micromouseonline/kronos/hesperus-timing-gate/docs/review.md

# Technical Review: KRONOS/CERBERUS Gate Firmware

`hesperus-timing-gate/firmware/src/main.cpp`

Reviewed by Claude

---

## Outstanding Features

### Disciplined dual-clock holdover architecture
The most technically sophisticated element of the firmware. By simultaneously capturing
both the Wi-Fi TSF counter and `esp_timer_get_time()` in the ISR at the moment of
the physical trigger, the design mirrors the holdover architecture of a professional
GPS receiver: a primary reference (TSF, disciplined by the AP's hardware beacon) and a
fallback oscillator (CPU crystal, disciplined by the EMA-filtered `clock_alpha`).
This is exactly the right approach for a wireless timing system where the primary
reference can momentarily disappear.

### EMA-filtered clock_alpha calibration
The 10%/90% EMA on `clock_alpha` is well-chosen. It suppresses per-beacon jitter while
still tracking slow crystal drift over minutes and hours. The >4 s inter-sample gate
ensures the ratio is statistically stable before being fed into the filter, avoiding
contamination from back-to-back events.

### MIN_PLAUSIBLE_TSF plausibility guard (300 000 000 µs)
Prevents accepting a TSF captured in the narrow window after a Wi-Fi stack reset before
beacon resynchronisation has occurred. 300 seconds is a well-judged threshold: long
enough to be certain the stack is settled, short enough to not delay legitimate startup.

### Escape hatch (PATCH 1) — proactive SYN recovery
After a successful `200 OK` response during SYN mode, the firmware immediately queries
the raw TSF and, if it looks healthy, forces re-entry by resetting `has_initial_baseline`.
This is a clean, proactive mechanism that does not rely on a new trigger event to
initiate recovery — important in a low-traffic test scenario where gate events may be
sparse.

### Explicit BSSID binding
`WiFi.begin(ssid, password, 0, bssid)` locks association to a known AP. Without this,
the ESP32 may roam to a neighbour access point whose TSF epoch is completely unrelated,
silently corrupting the timing baseline in a way that is very hard to diagnose in the
field.

### Prime heartbeat interval (5147 ms)
A non-round heartbeat interval desynchronises the transmission from 802.11 DTIM beacon
periods and from periodic tasks on other stations, reducing collision probability at the
AP — a detail that most implementors overlook.

### Correct FreeRTOS ISR practice
The beam-sample timer ISR (`onBeamSampleTimer`, `beam-sensor.h`'s dual-EMA
detector) does the minimum possible work: `vTaskNotifyGiveFromISR` followed
by `portYIELD_FROM_ISR()` when needed, nothing else. No ADC read, no float
math, and no queue push happen in ISR context — those are deferred to
`beamSampleTask`, woken by the notification, which does the `analogRead()`s,
runs the detector, and only then calls the plain (non-ISR) `xQueueSend()` to
hand a trigger off to `tsfCaptureTask`. Keeping the ISR to a bare notify is
the right call here specifically because the actual detection work (two
EMA updates plus a ratio compare) is too much to justify running inside an
ISR at all, unlike a simple GPIO edge capture.

### Hard Wi-Fi watchdog
`WiFi.disconnect(true, true)` + delay + `WiFi.begin()` completely tears down and
rebuilds the radio interface. A soft reconnect alone cannot recover certain ESP-IDF
lwIP crash states. This is the correct treatment for a 15-second silence.

---

## Summary Assessment

The dual-clock holdover design is genuinely impressive for a consumer-grade Wi-Fi
platform and represents a level of engineering depth that goes well beyond typical
ESP32 hobby projects. The empirical results (mean gap 2.36 µs, max 55 µs, 100%
pairing over 60,000 events) validate the architecture.

---

## Possible stress tests:

**Status update, 2026-08-06**: the beacon-spam campaign in
`NETWORK-TIMING-LOG.md` (spam-test sessions 2-15a) has since exercised
Layer 1 extensively — via deliberate beacon-frame flooding rather than the
HTTP-GET-flood method sketched below, but the same airtime-saturation
effect — and Layer 3 partially, via Bluetooth audio streaming co-tested
alongside the spammers (sessions 9-10, 15a) as a stand-in for channel
interference. Layers 2 (bulk throughput) and 4 (broadband noise) remain
genuinely untested and are deprioritized (`TODO.md`'s "Congested-airtime
stress testing" item) rather than actively planned. The sketches below are
left as originally written for reference.

  ### Layer 1 — Airtime saturation (your idea, refined)

  20 ESP32s each running a tight loop of HTTP GETs to a local server (a Pi or laptop running a trivial HTTP responder). 
  Set them all to the same SSID/BSSID as the timing gates. The goal is to pack the AP's transmit queue and force beacon 
  deferral — consumer APs do not protect beacon TBTTs under heavy load, so this directly stresses TSF jitter. Metrics 
  to watch: drift_variance in the audit log, and whether consecutive_audit_failures climbs.

  ### Layer 2 — Bulk throughput (saturate the medium)

  A Raspberry Pi (or any laptop) on the same AP running iperf3 -s, with another client doing iperf3 -c <ip> -t 300 
  generates sustained throughput that competes with every other station for airtime. Much higher per-device impact 
  than ESP32 GETs.

  ### Layer 3 — Channel interference (harder to ignore than load)

  A second cheap WiFi router (any old home router) configured to broadcast on an overlapping channel (e.g. your AP on ch 6, 
  the stressor on ch 4 or 8). This generates RF contention the AP cannot back off from, causing collision-driven retries 
  and beacon slippage. Very realistic simulation of a busy sports venue.

  ### Layer 4 — 2.4 GHz broadband noise

  A microwave oven running 30 cm from the AP is a surprisingly effective 2.4 GHz jammer — free if you have one, and 
  recreates the kind of environment you'd find at a car park or sports field.

  ### What to instrument

  The timing gate serial log already shows you drift_variance per event and consecutive_audit_failures. Add a counter 
  to the server side tracking how often mode=SYN appears in requests — that's your headline metric for how badly TSF sync 
  degrades under load. If you get to 5+ consecutive audit failures triggering forced re-baseline, the AP is struggling 
  to deliver beacons reliably.
  
---

## Future Development Path

Updated 2026-08-06: removed three rows that shipped since this table was
written (mDNS server discovery, HTTP keep-alive/WebSocket, and a
diagnostics HTTP server — see `docs/PROVISIONING.md`,
`NETWORK-TIMING-LOG.md`, and `firmware/src/net/debug-http-server.h`/
`network-health-stats.h` respectively) and trimmed "server URL" from the
NVS config store row for the same reason (cerberus's address is now
resolved dynamically via mDNS, not a config-store override). The
diagnostics server (`GET /logs`, `GET /status`, `GET`/`POST /status/reset`)
also covers part of what the old "field-deployable overflow-drop
notification" gap needed — lifetime stall/drop/disconnect counters now
persist across reboot (NVS) and are readable remotely, without a serial
cable attached.

| Phase | Feature | Notes |
|---|---|---|
| Near | Wi-Fi Modem Sleep | Extensively investigated, not just "unblocked" — see `NETWORK-TIMING-LOG.md`'s "Wi-Fi power-save vs. battery budget" issue (sessions 11-15a). `WIFI_PS_NONE` (`main.cpp:869`) stays the shipped default (decided 2026-08-04, ~110mA); `WIFI_PS_MIN_MODEM` saves ~35-40% power but has a real, still-unexplained stall/reliability regression under heavy congestion that got worse after one attempted mitigation. Still the highest-priority open item in that doc |
| Near | NVS config store | gate_id override, BEAM_CONFIRM_SAMPLES, DRIFT_MARGIN_US |
| Near | Configurable confirm-sample count | Per-channel `BEAM_CONFIRM_SAMPLES` (`beam-sensor.h`), loaded from NVS |
| Medium | OTA firmware update | ArduinoOTA or ESP-IDF OTA; critical for field deployment |
| Medium | SSD1306 display task | Gate ID, clock mode, last gap, queue depth (lib already in platformio.ini) |
| Medium | Stack telemetry in heartbeat | Append `&stack=NNN` to HB URL for remote diagnostics; scaffolding exists but is commented out (`main.cpp:510-512`) |
| Long | NVS event buffering | Survive power cycle with unsent events preserved in flash |
| Long | Multi-AP BSSID fallback | Secondary AP list with explicit TSF-resync on AP switch |
| Long | Local standalone scoring | Compute lap/split locally if server unreachable; display on SSD1306 |
| Long | Beam-sensor oversampling (DMA + decimate) | Raise ADC sample rate above 1kHz to reject 500-2000Hz pulsed-light aliasing; deferred 2026-09-09 after a bench trial at >4000lux ambient + heavy 1kHz pulsed interference showed reliable operation with the current 1kHz scheme. Revisit only if field trials later show it's still needed. Investigation notes (oversample-then-decimate via DMA, batched EMA catch-up design) captured for reuse if resumed |
