micromouseonline/kronos/references/ESP32-S3-TINY/ESP32-S3-Tiny-details-1-3cb57dcb7847e1db49d2faee9722d6df.webp

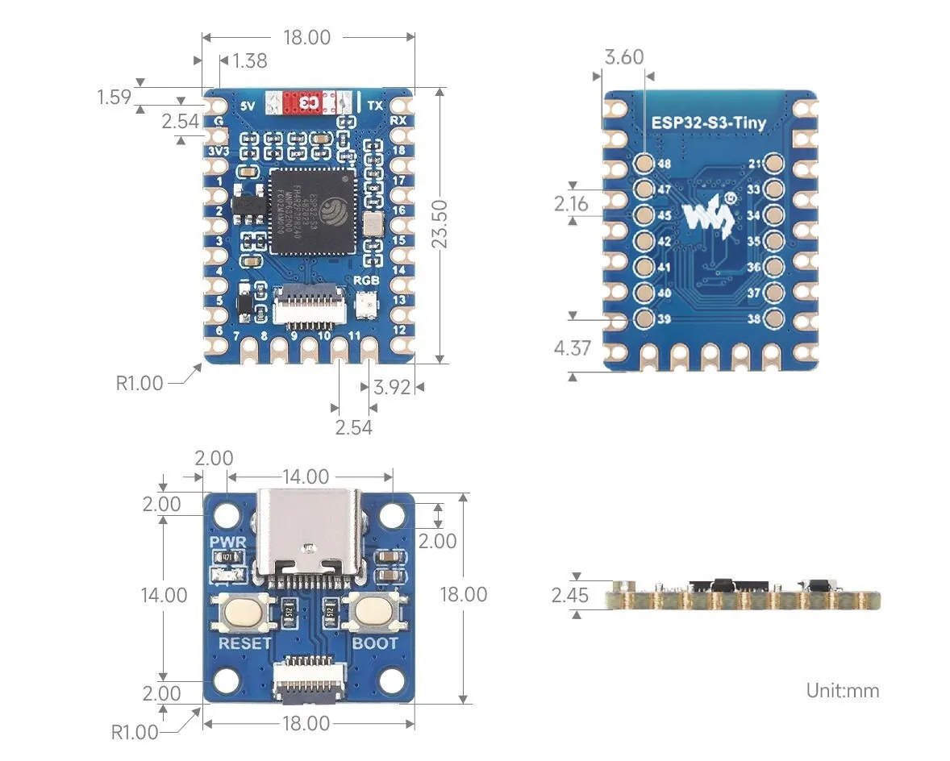
references/ESP32-S3-TINY/ESP32-S3-Tiny-details-1-3cb57dcb7847e1db49d2faee9722d6df.webp
