micromouseonline/kronos/references/ESP32-S3-TINY/ESP32-S3-Tiny-details-a4122450645a7c8208cc74ff0d9faf8f.webp

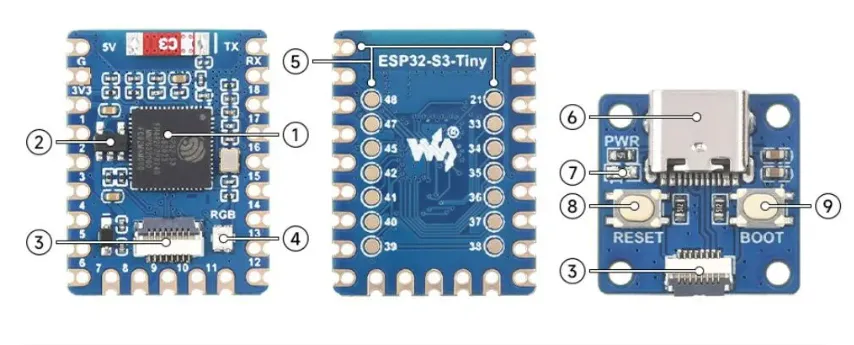
references/ESP32-S3-TINY/ESP32-S3-Tiny-details-a4122450645a7c8208cc74ff0d9faf8f.webp
