micromouseonline/kronos/references/QtPy-ESP32-PICO/adafruit_products_QTP_sch.png

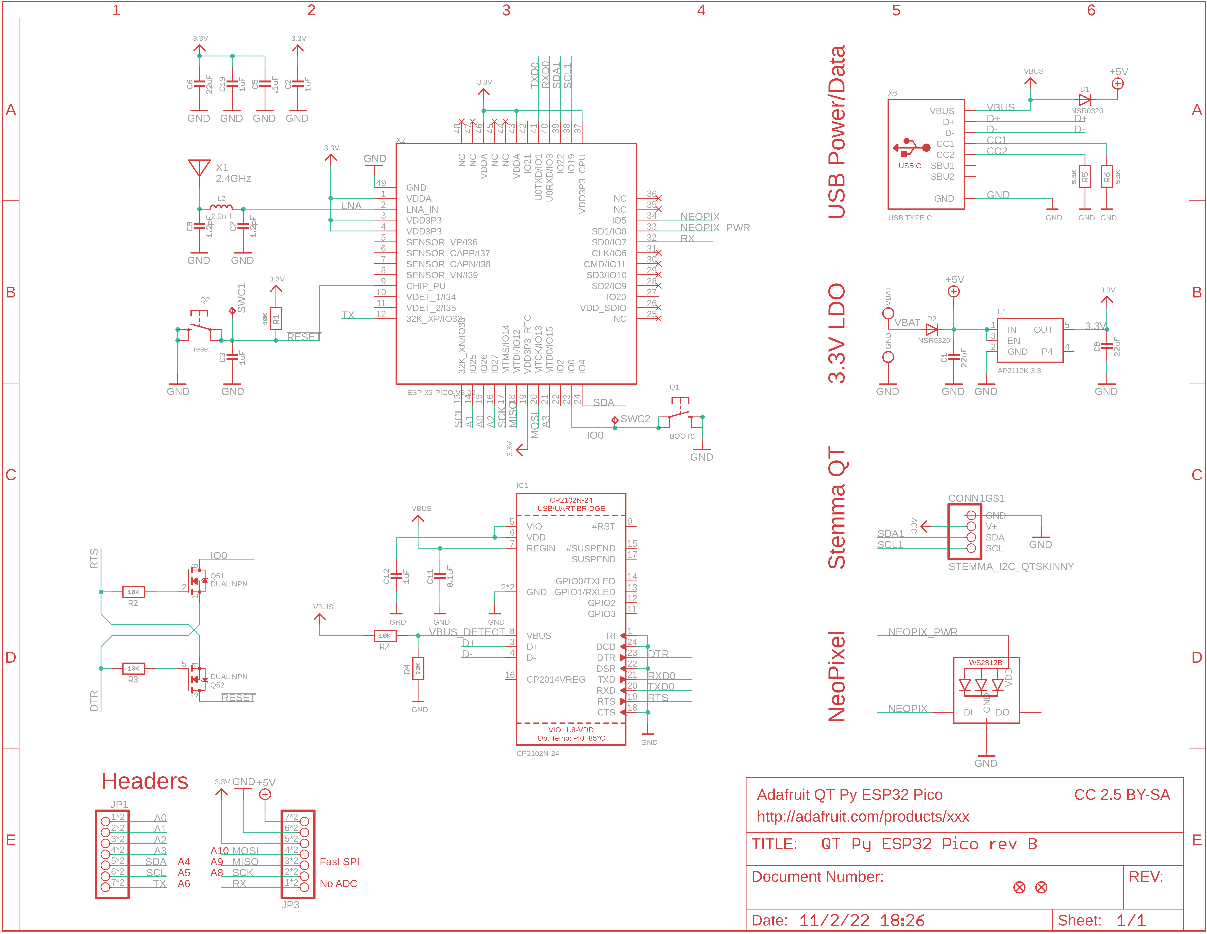
references/QtPy-ESP32-PICO/adafruit_products_QTP_sch.png
