micromouseonline/kronos/cerberus-gate-controller/hardware/mechanical/src/neokey-4x1.FCStd

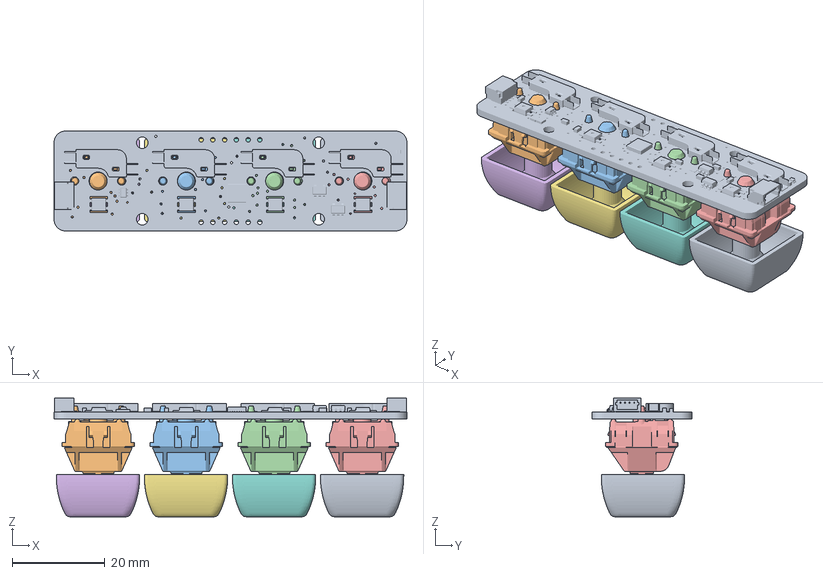
[picture p25: CAD file, 2026-09-06]
cerberus-gate-controller/hardware/mechanical/src/neokey-4x1.FCStd
76.2 x 21.6 x 25.6 mm
4980 NeoKey 1x4 QT
cherry-mx-switch
cherry-mx-switch001
cherry-mx-switch002
cherry-mx-switch003
mx-keycap-xda-18x18x9
mx-keycap-xda-18x18x001
mx-keycap-xda-18x18x002
mx-keycap-xda-18x18x003
