micromouseonline/kronos/hardware-shared/hesperus/exports/hesperus-wall-classic-nb11.stl

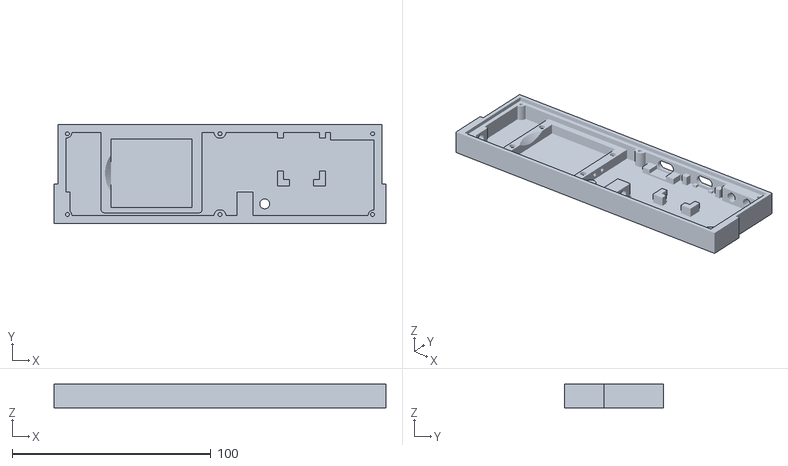
[picture p26: CAD file, 2026-09-10]
hardware-shared/hesperus/exports/hesperus-wall-classic-nb11.stl
167.0 x 50.0 x 12.0
