micromouseonline/kronos/cerberus-gate-controller/hardware/mechanical/exports/cherry-mx-switch.stl

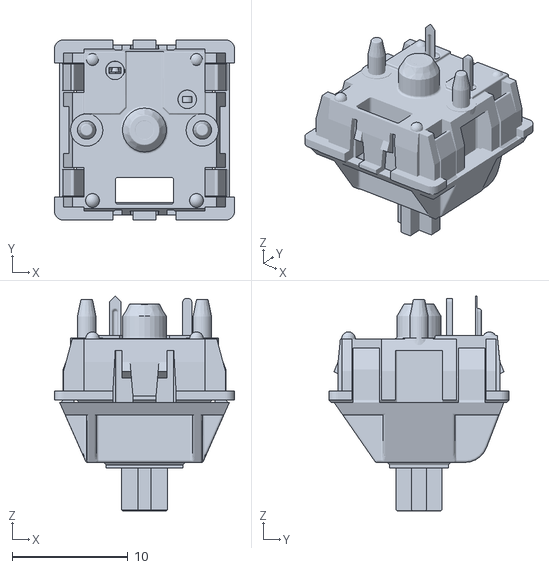
[picture p27: CAD file, 2026-09-06]
cerberus-gate-controller/hardware/mechanical/exports/cherry-mx-switch.stl
15.6 x 15.6 x 18.6
