micromouseonline/kronos/hardware-shared/hesperus/exports/hesperus-wall-classic-battery-cover.stl

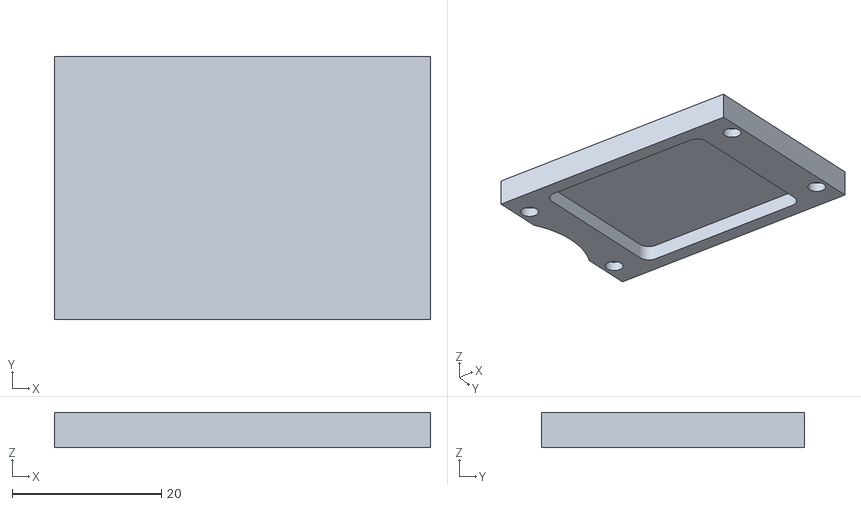
[picture p28: CAD file, 2026-09-10]
hardware-shared/hesperus/exports/hesperus-wall-classic-battery-cover.stl
50.3 x 35.2 x 4.75
