micromouseonline/kronos/cerberus-gate-controller/hardware/mechanical/exports/cerberus-case-back.stl

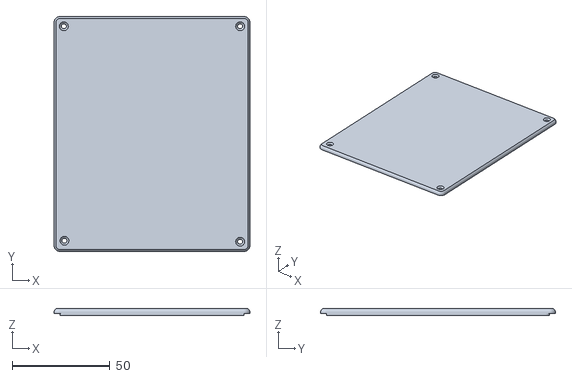
[picture p29: CAD file, 2026-09-06]
cerberus-gate-controller/hardware/mechanical/exports/cerberus-case-back.stl
100.0 x 120.0 x 3.50
