micromouseonline/kronos/hardware-shared/hesperus/exports/hesperus-wall-classic-cover-exit-hole-with-hatch.stl

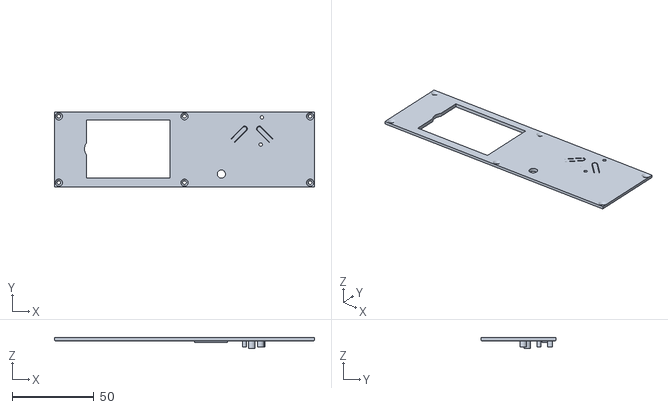
[picture p30: CAD file, 2026-09-10]
hardware-shared/hesperus/exports/hesperus-wall-classic-cover-exit-hole-with-hatch.stl
158.8 x 45.8 x 6.50
