micromouseonline/kronos/cerberus-gate-controller/hardware/mechanical/exports/cerberus-keycaps.3mf

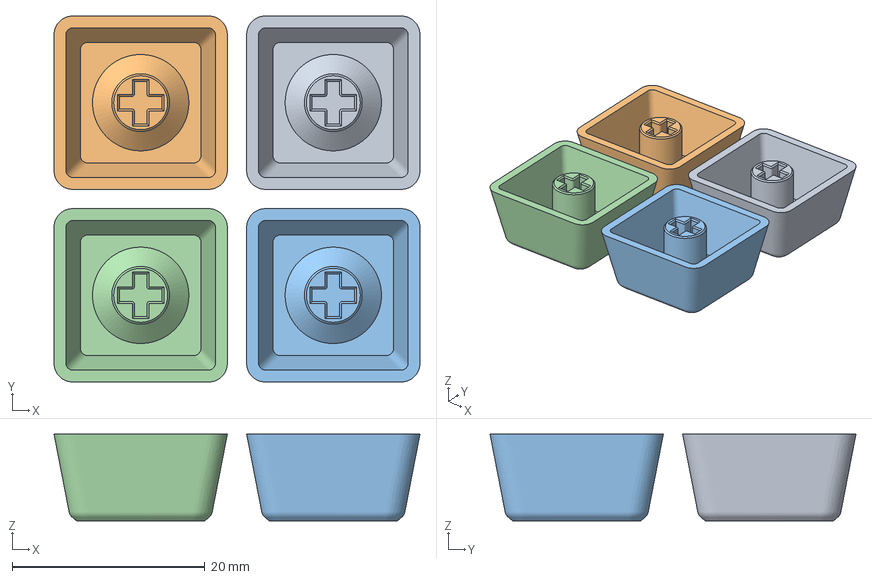
[picture p31: CAD file, 2026-09-06]
cerberus-gate-controller/hardware/mechanical/exports/cerberus-keycaps.3mf
38.0 x 38.0 x 9.00 mm
mx-xda-keycap-tapered-18x18x9.stl x 4
