micromouseonline/kronos/hardware-shared/hesperus/exports/hesperus-wall-classic-cover-no-hole.stl

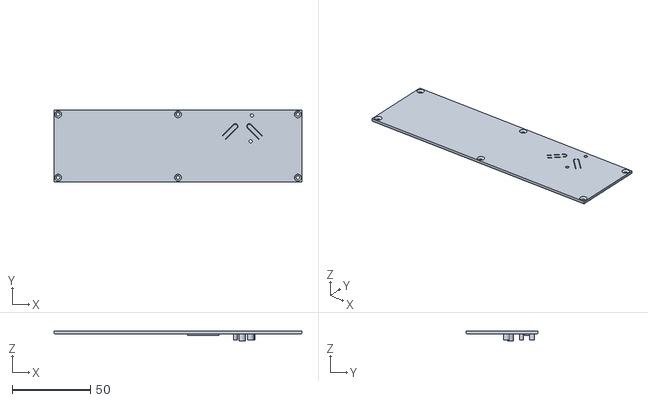
[picture p32: CAD file, 2026-09-07]
hardware-shared/hesperus/exports/hesperus-wall-classic-cover-no-hole.stl
158.8 x 45.8 x 6.50
