micromouseonline/kronos/cerberus-gate-controller/hardware/mechanical/exports/XDA_blank_rounded_keycaps.3mf

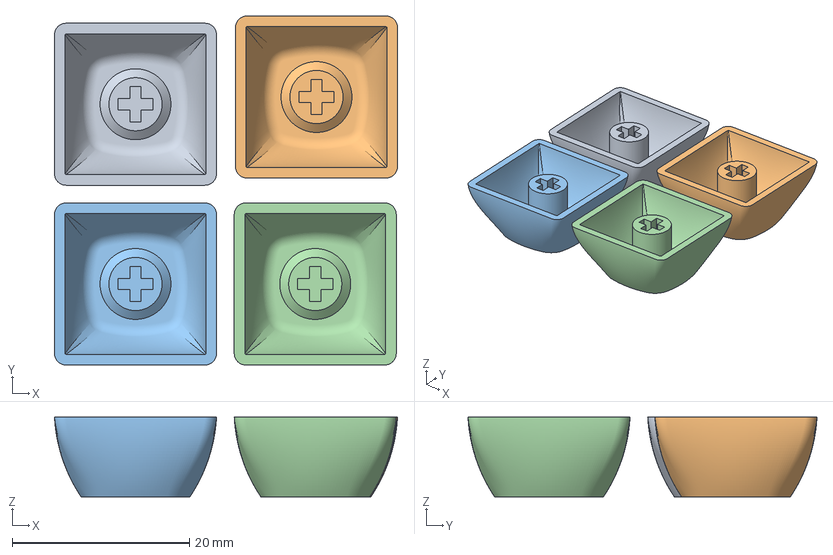
[picture p33: CAD file, 2026-09-06]
cerberus-gate-controller/hardware/mechanical/exports/XDA_blank_rounded_keycaps.3mf
38.7 x 39.4 x 9.00 mm
XDA_blank_rounded.stl x 4
