micromouseonline/kronos/hardware-shared/hesperus/exports/hesperus-wall-classic-end-tab.stl

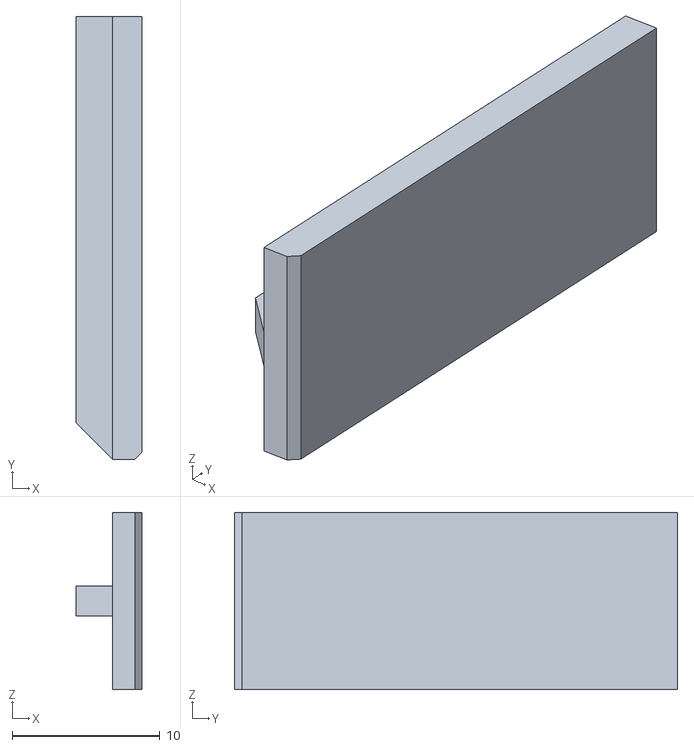
[picture p34: CAD file, 2026-09-07]
hardware-shared/hesperus/exports/hesperus-wall-classic-end-tab.stl
4.50 x 30.0 x 12.0
