micromouseonline/kronos/hardware-shared/hesperus/exports/hesperus-wall-classic-cap.stl

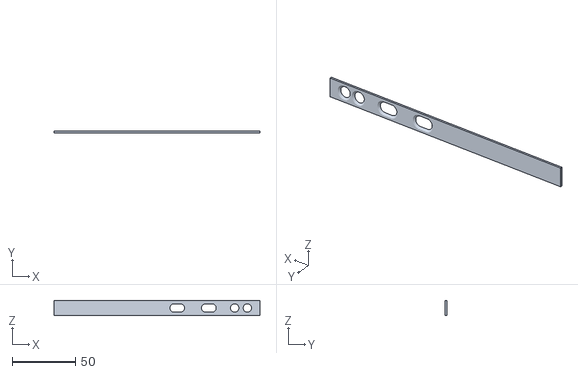
[picture p35: CAD file, 2026-09-07]
hardware-shared/hesperus/exports/hesperus-wall-classic-cap.stl
163.0 x 1.20 x 12.0
