micromouseonline/kronos/hardware-shared/hesperus/exports/hesperus-wall-classic-reflector.stl

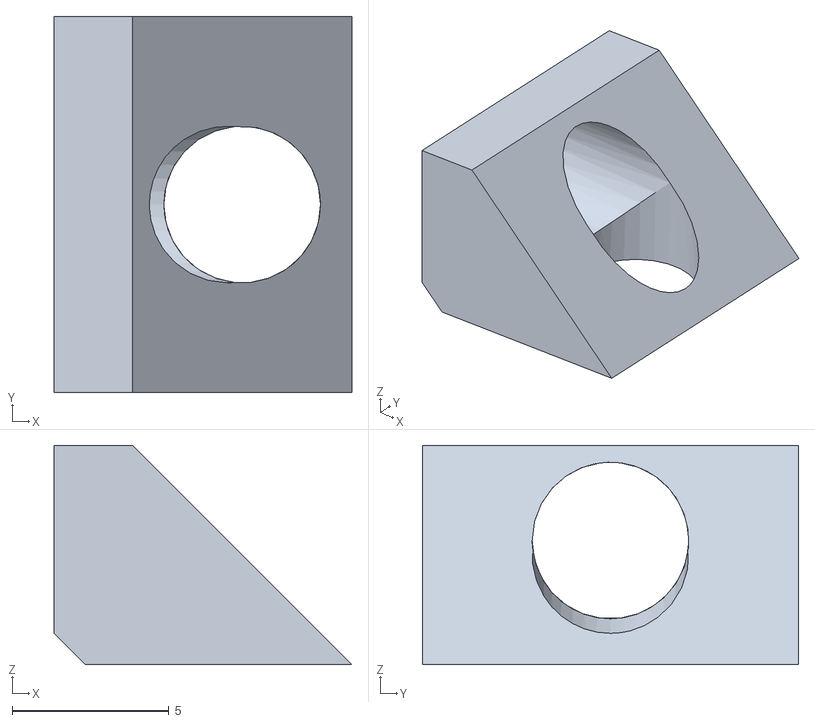
[picture p36: CAD file, 2026-09-07]
hardware-shared/hesperus/exports/hesperus-wall-classic-reflector.stl
9.50 x 12.0 x 7.00
