micromouseonline/kronos/hardware-shared/hesperus/exports/sensor-post-half-classic-2026.3mf

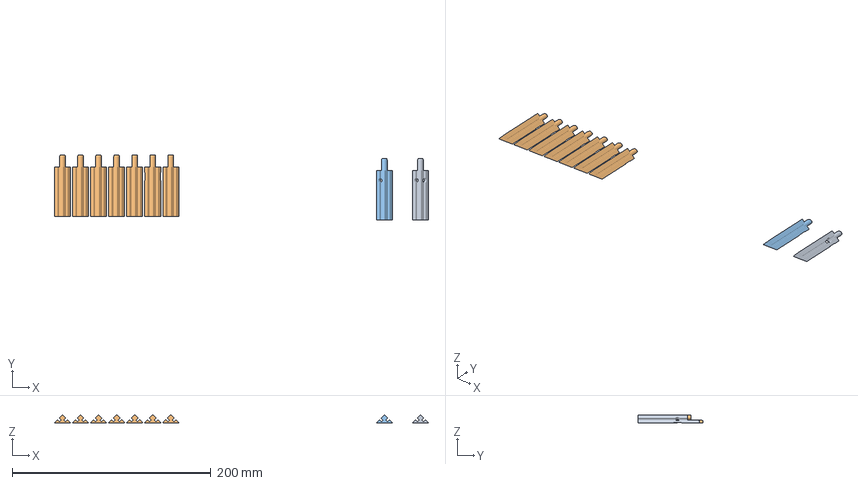
[picture p37: CAD file, 2026-09-07]
hardware-shared/hesperus/exports/sensor-post-half-classic-2026.3mf
376.4 x 65.7 x 8.20 mm
classic-sensor-post-half-2026-holes.stl
classic-sensor-post-half-2026-no-hole.stl x 7
classic-sensor-post-half-2026-single-hole.stl
