micromouseonline/kronos/test-data/arm-then-start-test-20260630-1522-analysis.txt

   #       recv_ms  event             tsf_us       gate_us  latency_ms
   0     229499098  ARM         229498826787    5816650070       271.2
   1     229499401  START       229499027257    5816850535       373.7
   2     229500100  ARM         229499826786    5817650064       273.2
   3     229500348  START       229500027260    5817850529       320.7
   4     229501091  ARM         229500826777    5818650056       264.2
   5     229501345  START       229501027252    5818850523       317.7
   6     229502094  ARM         229501826789    5819650052       267.2
   7     229502349  START       229502027255    5819850517       321.7
   8     229503093  ARM         229502826792    5820650045       266.2
   9     229503344  START       229503027254    5820850510       316.7
  10     229504091  ARM         229503826786    5821650039       264.2
  11     229504342  START       229504027252    5821850504       314.7
  12     229505093  ARM         229504826791    5822650033       266.2
  13     229505345  START       229505027253    5822850498       317.7
  14     229506089  ARM         229505826786    5823650027       262.2
  15     229506349  START       229506027234    5823850492       321.8
  16     229507091  ARM         229506826786    5824650020       264.2
  17     229507345  START       229507027251    5824850485       317.7
  18     229508093  ARM         229507826784    5825650014       266.2
  19     229508343  START       229508027251    5825850479       315.7
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
  min       313.8 ms
  max       373.7 ms
  p90       324.8 ms
  p95       325.8 ms
  p99       373.7 ms

-- all (n=198) --
  mean      293.1 ms
  median    295.0 ms
  stdev      27.1 ms
  min       262.2 ms
  max       373.7 ms
  p90       321.8 ms
  p95       324.8 ms
  p99       327.8 ms
