micromouseonline/kronos/test-data/arm-then-start-test-20260630-1522.txt

#[229499098] [HTTP] POST /api/event from 192.168.0.6 body={"gate_id":"UNKNOWN","event":"ARM","tsf_us":229498826787,"gate_us":5816650070}
#[229499401] [HTTP] POST /api/event from 192.168.0.6 body={"gate_id":"UNKNOWN","event":"START","tsf_us":229499027257,"gate_us":5816850535}
#[229500100] [HTTP] POST /api/event from 192.168.0.6 body={"gate_id":"UNKNOWN","event":"ARM","tsf_us":229499826786,"gate_us":5817650064}
#[229500348] [HTTP] POST /api/event from 192.168.0.6 body={"gate_id":"UNKNOWN","event":"START","tsf_us":229500027260,"gate_us":5817850529}
#[229501091] [HTTP] POST /api/event from 192.168.0.6 body={"gate_id":"UNKNOWN","event":"ARM","tsf_us":229500826777,"gate_us":5818650056}
#[229501345] [HTTP] POST /api/event from 192.168.0.6 body={"gate_id":"UNKNOWN","event":"START","tsf_us":229501027252,"gate_us":5818850523}
#[229502094] [HTTP] POST /api/event from 192.168.0.6 body={"gate_id":"UNKNOWN","event":"ARM","tsf_us":229501826789,"gate_us":5819650052}
#[229502349] [HTTP] POST /api/event from 192.168.0.6 body={"gate_id":"UNKNOWN","event":"START","tsf_us":229502027255,"gate_us":5819850517}
#[229503093] [HTTP] POST /api/event from 192.168.0.6 body={"gate_id":"UNKNOWN","event":"ARM","tsf_us":229502826792,"gate_us":5820650045}
#[229503344] [HTTP] POST /api/event from 192.168.0.6 body={"gate_id":"UNKNOWN","event":"START","tsf_us":229503027254,"gate_us":5820850510}
#[229504091] [HTTP] POST /api/event from 192.168.0.6 body={"gate_id":"UNKNOWN","event":"ARM","tsf_us":229503826786,"gate_us":5821650039}
#[229504342] [HTTP] POST /api/event from 192.168.0.6 body={"gate_id":"UNKNOWN","event":"START","tsf_us":229504027252,"gate_us":5821850504}
#[229505093] [HTTP] POST /api/event from 192.168.0.6 body={"gate_id":"UNKNOWN","event":"ARM","tsf_us":229504826791,"gate_us":5822650033}
#[229505345] [HTTP] POST /api/event from 192.168.0.6 body={"gate_id":"UNKNOWN","event":"START","tsf_us":229505027253,"gate_us":5822850498}
#[229506089] [HTTP] POST /api/event from 192.168.0.6 body={"gate_id":"UNKNOWN","event":"ARM","tsf_us":229505826786,"gate_us":5823650027}
#[229506349] [HTTP] POST /api/event from 192.168.0.6 body={"gate_id":"UNKNOWN","event":"START","tsf_us":229506027234,"gate_us":5823850492}
#[229507091] [HTTP] POST /api/event from 192.168.0.6 body={"gate_id":"UNKNOWN","event":"ARM","tsf_us":229506826786,"gate_us":5824650020}
#[229507345] [HTTP] POST /api/event from 192.168.0.6 body={"gate_id":"UNKNOWN","event":"START","tsf_us":229507027251,"gate_us":5824850485}
#[229508093] [HTTP] POST /api/event from 192.168.0.6 body={"gate_id":"UNKNOWN","event":"ARM","tsf_us":229507826784,"gate_us":5825650014}
#[229508343] [HTTP] POST /api/event from 192.168.0.6 body={"gate_id":"UNKNOWN","event":"START","tsf_us":229508027251,"gate_us":5825850479}
#[229509089] [HTTP] POST /api/event from 192.168.0.6 body={"gate_id":"UNKNOWN","event":"ARM","tsf_us":229508826781,"gate_us":5826650008}
#[229509344] [HTTP] POST /api/event from 192.168.0.6 body={"gate_id":"UNKNOWN","event":"START","tsf_us":229509027251,"gate_us":5826850473}
#[229510097] [HTTP] POST /api/event from 192.168.0.6 body={"gate_id":"UNKNOWN","event":"ARM","tsf_us":229509826782,"gate_us":5827650002}
#[229510353] [HTTP] POST /api/event from 192.168.0.6 body={"gate_id":"UNKNOWN","event":"START","tsf_us":229510027251,"gate_us":5827850466}
#[229511092] [HTTP] POST /api/event from 192.168.0.6 body={"gate_id":"UNKNOWN","event":"ARM","tsf_us":229510826782,"gate_us":5828649995}
#[229511344] [HTTP] POST /api/event from 192.168.0.6 body={"gate_id":"UNKNOWN","event":"START","tsf_us":229511027249,"gate_us":5828850460}
#[229512093] [HTTP] POST /api/event from 192.168.0.6 body={"gate_id":"UNKNOWN","event":"ARM","tsf_us":229511826786,"gate_us":5829649989}
#[229512343] [HTTP] POST /api/event from 192.168.0.6 body={"gate_id":"UNKNOWN","event":"START","tsf_us":229512027252,"gate_us":5829850454}
#[229513103] [HTTP] POST /api/event from 192.168.0.6 body={"gate_id":"UNKNOWN","event":"ARM","tsf_us":229512826786,"gate_us":5830649983}
#[229513341] [HTTP] POST /api/event from 192.168.0.6 body={"gate_id":"UNKNOWN","event":"START","tsf_us":229513027247,"gate_us":5830850448}
#[229514090] [HTTP] POST /api/event from 192.168.0.6 body={"gate_id":"UNKNOWN","event":"ARM","tsf_us":229513826780,"gate_us":5831649976}
#[229514346] [HTTP] POST /api/event from 192.168.0.6 body={"gate_id":"UNKNOWN","event":"START","tsf_us":229514027245,"gate_us":5831850441}
#[229515100] [HTTP] POST /api/event from 192.168.0.6 body={"gate_id":"UNKNOWN","event":"ARM","tsf_us":229514826780,"gate_us":5832649970}
#[229515355] [HTTP] POST /api/event from 192.168.0.6 body={"gate_id":"UNKNOWN","event":"START","tsf_us":229515027245,"gate_us":5832850435}
#[229516091] [HTTP] POST /api/event from 192.168.0.6 body={"gate_id":"UNKNOWN","event":"ARM","tsf_us":229515826777,"gate_us":5833649964}
#[229516344] [HTTP] POST /api/event from 192.168.0.6 body={"gate_id":"UNKNOWN","event":"START","tsf_us":229516027246,"gate_us":5833850429}
#[229517095] [HTTP] POST /api/event from 192.168.0.6 body={"gate_id":"UNKNOWN","event":"ARM","tsf_us":229516826776,"gate_us":5834649957}
#[229517344] [HTTP] POST /api/event from 192.168.0.6 body={"gate_id":"UNKNOWN","event":"START","tsf_us":229517027241,"gate_us":5834850422}
#[229518095] [HTTP] POST /api/event from 192.168.0.6 body={"gate_id":"UNKNOWN","event":"ARM","tsf_us":229517826782,"gate_us":5835649951}
#[229518346] [HTTP] POST /api/event from 192.168.0.6 body={"gate_id":"UNKNOWN","event":"START","tsf_us":229518027242,"gate_us":5835850416}
#[229519093] [HTTP] POST /api/event from 192.168.0.6 body={"gate_id":"UNKNOWN","event":"ARM","tsf_us":229518826782,"gate_us":5836649945}
#[229519347] [HTTP] POST /api/event from 192.168.0.6 body={"gate_id":"UNKNOWN","event":"START","tsf_us":229519027222,"gate_us":5836850409}
#[229520092] [HTTP] POST /api/event from 192.168.0.6 body={"gate_id":"UNKNOWN","event":"ARM","tsf_us":229519826775,"gate_us":5837649938}
#[229520346] [HTTP] POST /api/event from 192.168.0.6 body={"gate_id":"UNKNOWN","event":"START","tsf_us":229520027243,"gate_us":5837850403}
#[229521090] [HTTP] POST /api/event from 192.168.0.6 body={"gate_id":"UNKNOWN","event":"ARM","tsf_us":229520826774,"gate_us":5838649932}
#[229521346] [HTTP] POST /api/event from 192.168.0.6 body={"gate_id":"UNKNOWN","event":"START","tsf_us":229521027242,"gate_us":5838850397}
#[229522092] [HTTP] POST /api/event from 192.168.0.6 body={"gate_id":"UNKNOWN","event":"ARM","tsf_us":229521826775,"gate_us":5839649925}
#[229522346] [HTTP] POST /api/event from 192.168.0.6 body={"gate_id":"UNKNOWN","event":"START","tsf_us":229522027246,"gate_us":5839850390}
#[229523089] [HTTP] POST /api/event from 192.168.0.6 body={"gate_id":"UNKNOWN","event":"ARM","tsf_us":229522826774,"gate_us":5840649919}
#[229523345] [HTTP] POST /api/event from 192.168.0.6 body={"gate_id":"UNKNOWN","event":"START","tsf_us":229523027240,"gate_us":5840850384}
#[229524096] [HTTP] POST /api/event from 192.168.0.6 body={"gate_id":"UNKNOWN","event":"ARM","tsf_us":229523826774,"gate_us":5841649913}
#[229524345] [HTTP] POST /api/event from 192.168.0.6 body={"gate_id":"UNKNOWN","event":"START","tsf_us":229524027244,"gate_us":5841850378}
#[229525093] [HTTP] POST /api/event from 192.168.0.6 body={"gate_id":"UNKNOWN","event":"ARM","tsf_us":229524826777,"gate_us":5842649906}
#[229525349] [HTTP] POST /api/event from 192.168.0.6 body={"gate_id":"UNKNOWN","event":"START","tsf_us":229525027239,"gate_us":5842850371}
#[229526103] [HTTP] POST /api/event from 192.168.0.6 body={"gate_id":"UNKNOWN","event":"ARM","tsf_us":229525826773,"gate_us":5843649900}
#[229526346] [HTTP] POST /api/event from 192.168.0.6 body={"gate_id":"UNKNOWN","event":"START","tsf_us":229526027238,"gate_us":5843850365}
#[229527093] [HTTP] POST /api/event from 192.168.0.6 body={"gate_id":"UNKNOWN","event":"ARM","tsf_us":229526826766,"gate_us":5844649893}
#[229527344] [HTTP] POST /api/event from 192.168.0.6 body={"gate_id":"UNKNOWN","event":"START","tsf_us":229527027234,"gate_us":5844850358}
#[229528092] [HTTP] POST /api/event from 192.168.0.6 body={"gate_id":"UNKNOWN","event":"ARM","tsf_us":229527826770,"gate_us":5845649887}
#[229528346] [HTTP] POST /api/event from 192.168.0.6 body={"gate_id":"UNKNOWN","event":"START","tsf_us":229528027237,"gate_us":5845850352}
#[229529095] [HTTP] POST /api/event from 192.168.0.6 body={"gate_id":"UNKNOWN","event":"ARM","tsf_us":229528826769,"gate_us":5846649881}
#[229529345] [HTTP] POST /api/event from 192.168.0.6 body={"gate_id":"UNKNOWN","event":"START","tsf_us":229529027236,"gate_us":5846850346}
#[229530098] [HTTP] POST /api/event from 192.168.0.6 body={"gate_id":"UNKNOWN","event":"ARM","tsf_us":229529826768,"gate_us":5847649874}
#[229530347] [HTTP] POST /api/event from 192.168.0.6 body={"gate_id":"UNKNOWN","event":"START","tsf_us":229530027231,"gate_us":5847850339}
#[229531094] [HTTP] POST /api/event from 192.168.0.6 body={"gate_id":"UNKNOWN","event":"ARM","tsf_us":229530826772,"gate_us":5848649868}
#[229531349] [HTTP] POST /api/event from 192.168.0.6 body={"gate_id":"UNKNOWN","event":"START","tsf_us":229531027234,"gate_us":5848850333}
#[229532096] [HTTP] POST /api/event from 192.168.0.6 body={"gate_id":"UNKNOWN","event":"ARM","tsf_us":229531826765,"gate_us":5849649861}
#[229532352] [HTTP] POST /api/event from 192.168.0.6 body={"gate_id":"UNKNOWN","event":"START","tsf_us":229532027234,"gate_us":5849850326}
#[229533095] [HTTP] POST /api/event from 192.168.0.6 body={"gate_id":"UNKNOWN","event":"ARM","tsf_us":229532826769,"gate_us":5850649855}
#[229533350] [HTTP] POST /api/event from 192.168.0.6 body={"gate_id":"UNKNOWN","event":"START","tsf_us":229533027181,"gate_us":5850850320}
#[229534094] [HTTP] POST /api/event from 192.168.0.6 body={"gate_id":"UNKNOWN","event":"ARM","tsf_us":229533826762,"gate_us":5851649848}
#[229534341] [HTTP] POST /api/event from 192.168.0.6 body={"gate_id":"UNKNOWN","event":"START","tsf_us":229534027233,"gate_us":5851850313}
#[229535089] [HTTP] POST /api/event from 192.168.0.6 body={"gate_id":"UNKNOWN","event":"ARM","tsf_us":229534826766,"gate_us":5852649842}
#[229535345] [HTTP] POST /api/event from 192.168.0.6 body={"gate_id":"UNKNOWN","event":"START","tsf_us":229535027227,"gate_us":5852850307}
#[229536091] [HTTP] POST /api/event from 192.168.0.6 body={"gate_id":"UNKNOWN","event":"ARM","tsf_us":229535826765,"gate_us":5853649836}
#[229536349] [HTTP] POST /api/event from 192.168.0.6 body={"gate_id":"UNKNOWN","event":"START","tsf_us":229536027231,"gate_us":5853850301}
#[229537094] [HTTP] POST /api/event from 192.168.0.6 body={"gate_id":"UNKNOWN","event":"ARM","tsf_us":229536826753,"gate_us":5854649828}
#[229537347] [HTTP] POST /api/event from 192.168.0.6 body={"gate_id":"UNKNOWN","event":"START","tsf_us":229537027234,"gate_us":5854850294}
#[229538093] [HTTP] POST /api/event from 192.168.0.6 body={"gate_id":"UNKNOWN","event":"ARM","tsf_us":229537826762,"gate_us":5855649823}
#[229538346] [HTTP] POST /api/event from 192.168.0.6 body={"gate_id":"UNKNOWN","event":"START","tsf_us":229538027230,"gate_us":5855850288}
#[229539092] [HTTP] POST /api/event from 192.168.0.6 body={"gate_id":"UNKNOWN","event":"ARM","tsf_us":229538826762,"gate_us":5856649816}
#[229539344] [HTTP] POST /api/event from 192.168.0.6 body={"gate_id":"UNKNOWN","event":"START","tsf_us":229539027228,"gate_us":5856850281}
#[229540094] [HTTP] POST /api/event from 192.168.0.6 body={"gate_id":"UNKNOWN","event":"ARM","tsf_us":229539826760,"gate_us":5857649810}
#[229540344] [HTTP] POST /api/event from 192.168.0.6 body={"gate_id":"UNKNOWN","event":"START","tsf_us":229540027227,"gate_us":5857850275}
#[229541090] [HTTP] POST /api/event from 192.168.0.6 body={"gate_id":"UNKNOWN","event":"ARM","tsf_us":229540826758,"gate_us":5858649803}
#[229541347] [HTTP] POST /api/event from 192.168.0.6 body={"gate_id":"UNKNOWN","event":"START","tsf_us":229541027227,"gate_us":5858850268}
#[229542089] [HTTP] POST /api/event from 192.168.0.6 body={"gate_id":"UNKNOWN","event":"ARM","tsf_us":229541826758,"gate_us":5859649797}
#[229542346] [HTTP] POST /api/event from 192.168.0.6 body={"gate_id":"UNKNOWN","event":"START","tsf_us":229542027205,"gate_us":5859850262}
#[229543102] [HTTP] POST /api/event from 192.168.0.6 body={"gate_id":"UNKNOWN","event":"ARM","tsf_us":229542826756,"gate_us":5860649790}
#[229543345] [HTTP] POST /api/event from 192.168.0.6 body={"gate_id":"UNKNOWN","event":"START","tsf_us":229543027229,"gate_us":5860850255}
#[229544090] [HTTP] POST /api/event from 192.168.0.6 body={"gate_id":"UNKNOWN","event":"ARM","tsf_us":229543826762,"gate_us":5861649784}
#[229544343] [HTTP] POST /api/event from 192.168.0.6 body={"gate_id":"UNKNOWN","event":"START","tsf_us":229544027222,"gate_us":5861850249}
#[229545090] [HTTP] POST /api/event from 192.168.0.6 body={"gate_id":"UNKNOWN","event":"ARM","tsf_us":229544826762,"gate_us":5862649778}
#[229545343] [HTTP] POST /api/event from 192.168.0.6 body={"gate_id":"UNKNOWN","event":"START","tsf_us":229545027224,"gate_us":5862850242}
#[229546094] [HTTP] POST /api/event from 192.168.0.6 body={"gate_id":"UNKNOWN","event":"ARM","tsf_us":229545826756,"gate_us":5863649771}
#[229546351] [HTTP] POST /api/event from 192.168.0.6 body={"gate_id":"UNKNOWN","event":"START","tsf_us":229546027223,"gate_us":5863850236}
#[229547098] [HTTP] POST /api/event from 192.168.0.6 body={"gate_id":"UNKNOWN","event":"ARM","tsf_us":229546826760,"gate_us":5864649765}
#[229547344] [HTTP] POST /api/event from 192.168.0.6 body={"gate_id":"UNKNOWN","event":"START","tsf_us":229547027220,"gate_us":5864850230}
#[229548093] [HTTP] POST /api/event from 192.168.0.6 body={"gate_id":"UNKNOWN","event":"ARM","tsf_us":229547826753,"gate_us":5865649758}
#[229548353] [HTTP] POST /api/event from 192.168.0.6 body={"gate_id":"UNKNOWN","event":"START","tsf_us":229548027221,"gate_us":5865850223}
#[229549098] [HTTP] POST /api/event from 192.168.0.6 body={"gate_id":"UNKNOWN","event":"ARM","tsf_us":229548826758,"gate_us":5866649752}
#[229549352] [HTTP] POST /api/event from 192.168.0.6 body={"gate_id":"UNKNOWN","event":"START","tsf_us":229549027219,"gate_us":5866850217}
#[229550092] [HTTP] POST /api/event from 192.168.0.6 body={"gate_id":"UNKNOWN","event":"ARM","tsf_us":229549826754,"gate_us":5867649746}
#[229550347] [HTTP] POST /api/event from 192.168.0.6 body={"gate_id":"UNKNOWN","event":"START","tsf_us":229550027219,"gate_us":5867850210}
#[229551091] [HTTP] POST /api/event from 192.168.0.6 body={"gate_id":"UNKNOWN","event":"ARM","tsf_us":229550826753,"gate_us":5868649739}
#[229551349] [HTTP] POST /api/event from 192.168.0.6 body={"gate_id":"UNKNOWN","event":"START","tsf_us":229551027223,"gate_us":5868850204}
#[229552090] [HTTP] POST /api/event from 192.168.0.6 body={"gate_id":"UNKNOWN","event":"ARM","tsf_us":229551826756,"gate_us":5869649732}
#[229552348] [HTTP] POST /api/event from 192.168.0.6 body={"gate_id":"UNKNOWN","event":"START","tsf_us":229552027214,"gate_us":5869850197}
#[229553090] [HTTP] POST /api/event from 192.168.0.6 body={"gate_id":"UNKNOWN","event":"ARM","tsf_us":229552826755,"gate_us":5870649726}
#[229553345] [HTTP] POST /api/event from 192.168.0.6 body={"gate_id":"UNKNOWN","event":"START","tsf_us":229553027221,"gate_us":5870850191}
#[229554090] [HTTP] POST /api/event from 192.168.0.6 body={"gate_id":"UNKNOWN","event":"ARM","tsf_us":229553826750,"gate_us":5871649719}
#[229554347] [HTTP] POST /api/event from 192.168.0.6 body={"gate_id":"UNKNOWN","event":"START","tsf_us":229554027215,"gate_us":5871850184}
#[229555091] [HTTP] POST /api/event from 192.168.0.6 body={"gate_id":"UNKNOWN","event":"ARM","tsf_us":229554826748,"gate_us":5872649713}
#[229555343] [HTTP] POST /api/event from 192.168.0.6 body={"gate_id":"UNKNOWN","event":"START","tsf_us":229555027220,"gate_us":5872850178}
#[229556092] [HTTP] POST /api/event from 192.168.0.6 body={"gate_id":"UNKNOWN","event":"ARM","tsf_us":229555826752,"gate_us":5873649706}
#[229556342] [HTTP] POST /api/event from 192.168.0.6 body={"gate_id":"UNKNOWN","event":"START","tsf_us":229556027218,"gate_us":5873850171}
#[229557091] [HTTP] POST /api/event from 192.168.0.6 body={"gate_id":"UNKNOWN","event":"ARM","tsf_us":229556826743,"gate_us":5874649700}
#[229557346] [HTTP] POST /api/event from 192.168.0.6 body={"gate_id":"UNKNOWN","event":"START","tsf_us":229557027218,"gate_us":5874850165}
#[229558090] [HTTP] POST /api/event from 192.168.0.6 body={"gate_id":"UNKNOWN","event":"ARM","tsf_us":229557826742,"gate_us":5875649693}
#[229558343] [HTTP] POST /api/event from 192.168.0.6 body={"gate_id":"UNKNOWN","event":"START","tsf_us":229558027211,"gate_us":5875850158}
#[229559091] [HTTP] POST /api/event from 192.168.0.6 body={"gate_id":"UNKNOWN","event":"ARM","tsf_us":229558826746,"gate_us":5876649687}
#[229559345] [HTTP] POST /api/event from 192.168.0.6 body={"gate_id":"UNKNOWN","event":"START","tsf_us":229559027210,"gate_us":5876850152}
#[229560102] [HTTP] POST /api/event from 192.168.0.6 body={"gate_id":"UNKNOWN","event":"ARM","tsf_us":229559826745,"gate_us":5877649680}
#[229560347] [HTTP] POST /api/event from 192.168.0.6 body={"gate_id":"UNKNOWN","event":"START","tsf_us":229560027215,"gate_us":5877850145}
#[229561089] [HTTP] POST /api/event from 192.168.0.6 body={"gate_id":"UNKNOWN","event":"ARM","tsf_us":229560826744,"gate_us":5878649674}
#[229561341] [HTTP] POST /api/event from 192.168.0.6 body={"gate_id":"UNKNOWN","event":"START","tsf_us":229561027209,"gate_us":5878850139}
#[229562097] [HTTP] POST /api/event from 192.168.0.6 body={"gate_id":"UNKNOWN","event":"ARM","tsf_us":229561826742,"gate_us":5879649667}
#[229562355] [HTTP] POST /api/event from 192.168.0.6 body={"gate_id":"UNKNOWN","event":"START","tsf_us":229562027213,"gate_us":5879850132}
#[229563096] [HTTP] POST /api/event from 192.168.0.6 body={"gate_id":"UNKNOWN","event":"ARM","tsf_us":229562826736,"gate_us":5880649661}
#[229563352] [HTTP] POST /api/event from 192.168.0.6 body={"gate_id":"UNKNOWN","event":"START","tsf_us":229563027208,"gate_us":5880850127}
#[229564099] [HTTP] POST /api/event from 192.168.0.6 body={"gate_id":"UNKNOWN","event":"ARM","tsf_us":229563826739,"gate_us":5881649654}
#[229564344] [HTTP] POST /api/event from 192.168.0.6 body={"gate_id":"UNKNOWN","event":"START","tsf_us":229564027212,"gate_us":5881850119}
#[229565095] [HTTP] POST /api/event from 192.168.0.6 body={"gate_id":"UNKNOWN","event":"ARM","tsf_us":229564826737,"gate_us":5882649648}
#[229565346] [HTTP] POST /api/event from 192.168.0.6 body={"gate_id":"UNKNOWN","event":"START","tsf_us":229565027207,"gate_us":5882850113}
#[229566092] [HTTP] POST /api/event from 192.168.0.6 body={"gate_id":"UNKNOWN","event":"ARM","tsf_us":229565826739,"gate_us":5883649641}
#[229566349] [HTTP] POST /api/event from 192.168.0.6 body={"gate_id":"UNKNOWN","event":"START","tsf_us":229566027205,"gate_us":5883850106}
#[229567091] [HTTP] POST /api/event from 192.168.0.6 body={"gate_id":"UNKNOWN","event":"ARM","tsf_us":229566826740,"gate_us":5884649635}
#[229567345] [HTTP] POST /api/event from 192.168.0.6 body={"gate_id":"UNKNOWN","event":"START","tsf_us":229567027202,"gate_us":5884850099}
#[229568095] [HTTP] POST /api/event from 192.168.0.6 body={"gate_id":"UNKNOWN","event":"ARM","tsf_us":229567826734,"gate_us":5885649628}
#[229568346] [HTTP] POST /api/event from 192.168.0.6 body={"gate_id":"UNKNOWN","event":"START","tsf_us":229568027204,"gate_us":5885850093}
#[229569094] [HTTP] POST /api/event from 192.168.0.6 body={"gate_id":"UNKNOWN","event":"ARM","tsf_us":229568826737,"gate_us":5886649621}
#[229569343] [HTTP] POST /api/event from 192.168.0.6 body={"gate_id":"UNKNOWN","event":"START","tsf_us":229569027203,"gate_us":5886850086}
#[229570092] [HTTP] POST /api/event from 192.168.0.6 body={"gate_id":"UNKNOWN","event":"ARM","tsf_us":229569826734,"gate_us":5887649615}
#[229570345] [HTTP] POST /api/event from 192.168.0.6 body={"gate_id":"UNKNOWN","event":"START","tsf_us":229570027202,"gate_us":5887850080}
#[229571092] [HTTP] POST /api/event from 192.168.0.6 body={"gate_id":"UNKNOWN","event":"ARM","tsf_us":229570826735,"gate_us":5888649608}
#[229571345] [HTTP] POST /api/event from 192.168.0.6 body={"gate_id":"UNKNOWN","event":"START","tsf_us":229571027201,"gate_us":5888850073}
#[229572091] [HTTP] POST /api/event from 192.168.0.6 body={"gate_id":"UNKNOWN","event":"ARM","tsf_us":229571826736,"gate_us":5889649602}
#[229572343] [HTTP] POST /api/event from 192.168.0.6 body={"gate_id":"UNKNOWN","event":"START","tsf_us":229572027198,"gate_us":5889850067}
#[229573090] [HTTP] POST /api/event from 192.168.0.6 body={"gate_id":"UNKNOWN","event":"ARM","tsf_us":229572826721,"gate_us":5890649595}
#[229573342] [HTTP] POST /api/event from 192.168.0.6 body={"gate_id":"UNKNOWN","event":"START","tsf_us":229573027198,"gate_us":5890850060}
#[229574094] [HTTP] POST /api/event from 192.168.0.6 body={"gate_id":"UNKNOWN","event":"ARM","tsf_us":229573826736,"gate_us":5891649589}
#[229574345] [HTTP] POST /api/event from 192.168.0.6 body={"gate_id":"UNKNOWN","event":"START","tsf_us":229574027198,"gate_us":5891850054}
#[229575093] [HTTP] POST /api/event from 192.168.0.6 body={"gate_id":"UNKNOWN","event":"ARM","tsf_us":229574826735,"gate_us":5892649582}
#[229575347] [HTTP] POST /api/event from 192.168.0.6 body={"gate_id":"UNKNOWN","event":"START","tsf_us":229575027194,"gate_us":5892850047}
#[229576093] [HTTP] POST /api/event from 192.168.0.6 body={"gate_id":"UNKNOWN","event":"ARM","tsf_us":229575826735,"gate_us":5893649576}
#[229576346] [HTTP] POST /api/event from 192.168.0.6 body={"gate_id":"UNKNOWN","event":"START","tsf_us":229576027201,"gate_us":5893850041}
#[229577099] [HTTP] POST /api/event from 192.168.0.6 body={"gate_id":"UNKNOWN","event":"ARM","tsf_us":229576826729,"gate_us":5894649569}
#[229577349] [HTTP] POST /api/event from 192.168.0.6 body={"gate_id":"UNKNOWN","event":"START","tsf_us":229577027200,"gate_us":5894850034}
#[229578095] [HTTP] POST /api/event from 192.168.0.6 body={"gate_id":"UNKNOWN","event":"ARM","tsf_us":229577826733,"gate_us":5895649563}
#[229578345] [HTTP] POST /api/event from 192.168.0.6 body={"gate_id":"UNKNOWN","event":"START","tsf_us":229578027175,"gate_us":5895850027}
#[229579101] [HTTP] POST /api/event from 192.168.0.6 body={"gate_id":"UNKNOWN","event":"ARM","tsf_us":229578826727,"gate_us":5896649556}
#[229579353] [HTTP] POST /api/event from 192.168.0.6 body={"gate_id":"UNKNOWN","event":"START","tsf_us":229579027193,"gate_us":5896850021}
#[229580091] [HTTP] POST /api/event from 192.168.0.6 body={"gate_id":"UNKNOWN","event":"ARM","tsf_us":229579826728,"gate_us":5897649549}
#[229580342] [HTTP] POST /api/event from 192.168.0.6 body={"gate_id":"UNKNOWN","event":"START","tsf_us":229580027193,"gate_us":5897850014}
#[229581094] [HTTP] POST /api/event from 192.168.0.6 body={"gate_id":"UNKNOWN","event":"ARM","tsf_us":229580826723,"gate_us":5898649543}
#[229581347] [HTTP] POST /api/event from 192.168.0.6 body={"gate_id":"UNKNOWN","event":"START","tsf_us":229581027197,"gate_us":5898850008}
#[229582094] [HTTP] POST /api/event from 192.168.0.6 body={"gate_id":"UNKNOWN","event":"ARM","tsf_us":229581826745,"gate_us":5899649538}
#[229582346] [HTTP] POST /api/event from 192.168.0.6 body={"gate_id":"UNKNOWN","event":"START","tsf_us":229582027195,"gate_us":5899850001}
#[229583089] [HTTP] POST /api/event from 192.168.0.6 body={"gate_id":"UNKNOWN","event":"ARM","tsf_us":229582826724,"gate_us":5900649530}
#[229583349] [HTTP] POST /api/event from 192.168.0.6 body={"gate_id":"UNKNOWN","event":"START","tsf_us":229583027192,"gate_us":5900849995}
#[229584090] [HTTP] POST /api/event from 192.168.0.6 body={"gate_id":"UNKNOWN","event":"ARM","tsf_us":229583826727,"gate_us":5901649523}
#[229584347] [HTTP] POST /api/event from 192.168.0.6 body={"gate_id":"UNKNOWN","event":"START","tsf_us":229584027193,"gate_us":5901849988}
#[229585094] [HTTP] POST /api/event from 192.168.0.6 body={"gate_id":"UNKNOWN","event":"ARM","tsf_us":229584826723,"gate_us":5902649517}
#[229585344] [HTTP] POST /api/event from 192.168.0.6 body={"gate_id":"UNKNOWN","event":"START","tsf_us":229585027188,"gate_us":5902849982}
#[229586089] [HTTP] POST /api/event from 192.168.0.6 body={"gate_id":"UNKNOWN","event":"ARM","tsf_us":229585826721,"gate_us":5903649510}
#[229586347] [HTTP] POST /api/event from 192.168.0.6 body={"gate_id":"UNKNOWN","event":"START","tsf_us":229586027188,"gate_us":5903849975}
#[229587092] [HTTP] POST /api/event from 192.168.0.6 body={"gate_id":"UNKNOWN","event":"ARM","tsf_us":229586826721,"gate_us":5904649503}
#[229587346] [HTTP] POST /api/event from 192.168.0.6 body={"gate_id":"UNKNOWN","event":"START","tsf_us":229587027191,"gate_us":5904849968}
#[229588091] [HTTP] POST /api/event from 192.168.0.6 body={"gate_id":"UNKNOWN","event":"ARM","tsf_us":229587826720,"gate_us":5905649497}
#[229588344] [HTTP] POST /api/event from 192.168.0.6 body={"gate_id":"UNKNOWN","event":"START","tsf_us":229588027190,"gate_us":5905849962}
#[229589091] [HTTP] POST /api/event from 192.168.0.6 body={"gate_id":"UNKNOWN","event":"ARM","tsf_us":229588826720,"gate_us":5906649490}
#[229589352] [HTTP] POST /api/event from 192.168.0.6 body={"gate_id":"UNKNOWN","event":"START","tsf_us":229589027185,"gate_us":5906849955}
#[229590095] [HTTP] POST /api/event from 192.168.0.6 body={"gate_id":"UNKNOWN","event":"ARM","tsf_us":229589826716,"gate_us":5907649484}
#[229590351] [HTTP] POST /api/event from 192.168.0.6 body={"gate_id":"UNKNOWN","event":"START","tsf_us":229590027183,"gate_us":5907849949}
#[229591090] [HTTP] POST /api/event from 192.168.0.6 body={"gate_id":"UNKNOWN","event":"ARM","tsf_us":229590826716,"gate_us":5908649477}
#[229591347] [HTTP] POST /api/event from 192.168.0.6 body={"gate_id":"UNKNOWN","event":"START","tsf_us":229591027183,"gate_us":5908849942}
#[229592091] [HTTP] POST /api/event from 192.168.0.6 body={"gate_id":"UNKNOWN","event":"ARM","tsf_us":229591826716,"gate_us":5909649471}
#[229592345] [HTTP] POST /api/event from 192.168.0.6 body={"gate_id":"UNKNOWN","event":"START","tsf_us":229592027183,"gate_us":5909849936}
#[229593092] [HTTP] POST /api/event from 192.168.0.6 body={"gate_id":"UNKNOWN","event":"ARM","tsf_us":229592826719,"gate_us":5910649464}
#[229593344] [HTTP] POST /api/event from 192.168.0.6 body={"gate_id":"UNKNOWN","event":"START","tsf_us":229593027181,"gate_us":5910849929}
#[229594098] [HTTP] POST /api/event from 192.168.0.6 body={"gate_id":"UNKNOWN","event":"ARM","tsf_us":229593826707,"gate_us":5911649457}
#[229594345] [HTTP] POST /api/event from 192.168.0.6 body={"gate_id":"UNKNOWN","event":"START","tsf_us":229594027185,"gate_us":5911849922}
#[229595095] [HTTP] POST /api/event from 192.168.0.6 body={"gate_id":"UNKNOWN","event":"ARM","tsf_us":229594826717,"gate_us":5912649451}
#[229595349] [HTTP] POST /api/event from 192.168.0.6 body={"gate_id":"UNKNOWN","event":"START","tsf_us":229595027183,"gate_us":5912849916}
#[229596096] [HTTP] POST /api/event from 192.168.0.6 body={"gate_id":"UNKNOWN","event":"ARM","tsf_us":229595826717,"gate_us":5913649444}
#[229596355] [HTTP] POST /api/event from 192.168.0.6 body={"gate_id":"UNKNOWN","event":"START","tsf_us":229596027179,"gate_us":5913849909}
#[229597091] [HTTP] POST /api/event from 192.168.0.6 body={"gate_id":"UNKNOWN","event":"ARM","tsf_us":229596826716,"gate_us":5914649438}
#[229597345] [HTTP] POST /api/event from 192.168.0.6 body={"gate_id":"UNKNOWN","event":"START","tsf_us":229597027182,"gate_us":5914849903}
