micromouseonline/kronos/hesperus-timing-gate/docs/test-data.md

# Sample data from the timing gate.

These are readings of the slow filter outputs from the start gate under various lighting conditions

## A. Ambient illumination only - diffuse daylight at about 150lux. No emitter.

armSlow: 0.0
startSlow: 0.2

NOTE: Both filters show uncorrelated periods where the slow filter can rise to around 12 counts even thoughthe input (raw value) remains at zero.

## B. Ambient illumination as before but with oerhead LED lighting raising the level to about 350lux. No emitter

armSlow: 0.0
startSlow: 0.1

NOTE: the slow filter output displays the same anomalous behaviour.

## C. As case B but with emitters turned on.

armSlow: 870
startSlow: 450

NOTE: anomalous behaviour persists with the same amplitude as before

## D. As case C but with additional ambient provided by incandescent lighting brings ambient up to about 2200lux

armSlow: 1160
startSlow: 760

NOTE: same anomalies.
