micromouseonline/kronos/test-data/latency-test-20260720-1430.txt

#[228636424] [HTTP] POST /api/event from 192.168.0.189 body={"gate_id":"UNKNOWN","event":"GOAL","tsf_us":228635597374,"gate_us":4965081820}
#[228636680] [HTTP] POST /api/event from 192.168.0.189 body={"gate_id":"UNKNOWN","event":"GOAL","tsf_us":228636597379,"gate_us":4966081815}
#[228637868] [HTTP] POST /api/event from 192.168.0.189 body={"gate_id":"UNKNOWN","event":"GOAL","tsf_us":228637597379,"gate_us":4967081810}
#[228638869] [HTTP] POST /api/event from 192.168.0.189 body={"gate_id":"UNKNOWN","event":"GOAL","tsf_us":228638597377,"gate_us":4968081805}
#[228639864] [HTTP] POST /api/event from 192.168.0.189 body={"gate_id":"UNKNOWN","event":"GOAL","tsf_us":228639597380,"gate_us":4969081800}
#[228640867] [HTTP] POST /api/event from 192.168.0.189 body={"gate_id":"UNKNOWN","event":"GOAL","tsf_us":228640597376,"gate_us":4970081796}
#[228641865] [HTTP] POST /api/event from 192.168.0.189 body={"gate_id":"UNKNOWN","event":"GOAL","tsf_us":228641597374,"gate_us":4971081791}
#[228642864] [HTTP] POST /api/event from 192.168.0.189 body={"gate_id":"UNKNOWN","event":"GOAL","tsf_us":228642597378,"gate_us":4972081786}
#[228643866] [HTTP] POST /api/event from 192.168.0.189 body={"gate_id":"UNKNOWN","event":"GOAL","tsf_us":228643597377,"gate_us":4973081781}
#[228644861] [HTTP] POST /api/event from 192.168.0.189 body={"gate_id":"UNKNOWN","event":"GOAL","tsf_us":228644597378,"gate_us":4974081776}
#[228645863] [HTTP] POST /api/event from 192.168.0.189 body={"gate_id":"UNKNOWN","event":"GOAL","tsf_us":228645597378,"gate_us":4975081772}
#[228646863] [HTTP] POST /api/event from 192.168.0.189 body={"gate_id":"UNKNOWN","event":"GOAL","tsf_us":228646597379,"gate_us":4976081767}
#[228647864] [HTTP] POST /api/event from 192.168.0.189 body={"gate_id":"UNKNOWN","event":"GOAL","tsf_us":228647597374,"gate_us":4977081762}
#[228648866] [HTTP] POST /api/event from 192.168.0.189 body={"gate_id":"UNKNOWN","event":"GOAL","tsf_us":228648597373,"gate_us":4978081757}
#[228649873] [HTTP] POST /api/event from 192.168.0.189 body={"gate_id":"UNKNOWN","event":"GOAL","tsf_us":228649597377,"gate_us":4979081752}
#[228650866] [HTTP] POST /api/event from 192.168.0.189 body={"gate_id":"UNKNOWN","event":"GOAL","tsf_us":228650597370,"gate_us":4980081747}
#[228651863] [HTTP] POST /api/event from 192.168.0.189 body={"gate_id":"UNKNOWN","event":"GOAL","tsf_us":228651597376,"gate_us":4981081743}
#[228652865] [HTTP] POST /api/event from 192.168.0.189 body={"gate_id":"UNKNOWN","event":"GOAL","tsf_us":228652597376,"gate_us":4982081738}
#[228653867] [HTTP] POST /api/event from 192.168.0.189 body={"gate_id":"UNKNOWN","event":"GOAL","tsf_us":228653597376,"gate_us":4983081733}
#[228654870] [HTTP] POST /api/event from 192.168.0.189 body={"gate_id":"UNKNOWN","event":"GOAL","tsf_us":228654597374,"gate_us":4984081728}
#[228655872] [HTTP] POST /api/event from 192.168.0.189 body={"gate_id":"UNKNOWN","event":"GOAL","tsf_us":228655597374,"gate_us":4985081723}
#[228656865] [HTTP] POST /api/event from 192.168.0.189 body={"gate_id":"UNKNOWN","event":"GOAL","tsf_us":228656597375,"gate_us":4986081718}
#[228657870] [HTTP] POST /api/event from 192.168.0.189 body={"gate_id":"UNKNOWN","event":"GOAL","tsf_us":228657597369,"gate_us":4987081713}
#[228658861] [HTTP] POST /api/event from 192.168.0.189 body={"gate_id":"UNKNOWN","event":"GOAL","tsf_us":228658597374,"gate_us":4988081709}
#[228659867] [HTTP] POST /api/event from 192.168.0.189 body={"gate_id":"UNKNOWN","event":"GOAL","tsf_us":228659597373,"gate_us":4989081704}
#[228660864] [HTTP] POST /api/event from 192.168.0.189 body={"gate_id":"UNKNOWN","event":"GOAL","tsf_us":228660597364,"gate_us":4990081699}
#[228661862] [HTTP] POST /api/event from 192.168.0.189 body={"gate_id":"UNKNOWN","event":"GOAL","tsf_us":228661597372,"gate_us":4991081694}
#[228662877] [HTTP] POST /api/event from 192.168.0.189 body={"gate_id":"UNKNOWN","event":"GOAL","tsf_us":228662597372,"gate_us":4992081689}
#[228663903] [HTTP] POST /api/event from 192.168.0.189 body={"gate_id":"UNKNOWN","event":"GOAL","tsf_us":228663597373,"gate_us":4993081684}
#[228664863] [HTTP] POST /api/event from 192.168.0.189 body={"gate_id":"UNKNOWN","event":"GOAL","tsf_us":228664597369,"gate_us":4994081679}
#[228665881] [HTTP] POST /api/event from 192.168.0.189 body={"gate_id":"UNKNOWN","event":"GOAL","tsf_us":228665597352,"gate_us":4995081673}
#[228666874] [HTTP] POST /api/event from 192.168.0.189 body={"gate_id":"UNKNOWN","event":"GOAL","tsf_us":228666597367,"gate_us":4996081669}
#[228667863] [HTTP] POST /api/event from 192.168.0.189 body={"gate_id":"UNKNOWN","event":"GOAL","tsf_us":228667597368,"gate_us":4997081664}
#[228668882] [HTTP] POST /api/event from 192.168.0.189 body={"gate_id":"UNKNOWN","event":"GOAL","tsf_us":228668597370,"gate_us":4998081660}
#[228669863] [HTTP] POST /api/event from 192.168.0.189 body={"gate_id":"UNKNOWN","event":"GOAL","tsf_us":228669597369,"gate_us":4999081655}
#[228670877] [HTTP] POST /api/event from 192.168.0.189 body={"gate_id":"UNKNOWN","event":"GOAL","tsf_us":228670597370,"gate_us":5000081650}
#[228671867] [HTTP] POST /api/event from 192.168.0.189 body={"gate_id":"UNKNOWN","event":"GOAL","tsf_us":228671597368,"gate_us":5001081645}
#[228672863] [HTTP] POST /api/event from 192.168.0.189 body={"gate_id":"UNKNOWN","event":"GOAL","tsf_us":228672597366,"gate_us":5002081640}
#[228673866] [HTTP] POST /api/event from 192.168.0.189 body={"gate_id":"UNKNOWN","event":"GOAL","tsf_us":228673597369,"gate_us":5003081635}
#[228674866] [HTTP] POST /api/event from 192.168.0.189 body={"gate_id":"UNKNOWN","event":"GOAL","tsf_us":228674597367,"gate_us":5004081630}
#[228675862] [HTTP] POST /api/event from 192.168.0.189 body={"gate_id":"UNKNOWN","event":"GOAL","tsf_us":228675597366,"gate_us":5005081625}
#[228676865] [HTTP] POST /api/event from 192.168.0.189 body={"gate_id":"UNKNOWN","event":"GOAL","tsf_us":228676597365,"gate_us":5006081620}
#[228677866] [HTTP] POST /api/event from 192.168.0.189 body={"gate_id":"UNKNOWN","event":"GOAL","tsf_us":228677597368,"gate_us":5007081615}
#[228678943] [HTTP] POST /api/event from 192.168.0.189 body={"gate_id":"UNKNOWN","event":"GOAL","tsf_us":228678597365,"gate_us":5008081610}
#[228679903] [HTTP] POST /api/event from 192.168.0.189 body={"gate_id":"UNKNOWN","event":"GOAL","tsf_us":228679597366,"gate_us":5009081605}
#[228680867] [HTTP] POST /api/event from 192.168.0.189 body={"gate_id":"UNKNOWN","event":"GOAL","tsf_us":228680597369,"gate_us":5010081600}
#[228681865] [HTTP] POST /api/event from 192.168.0.189 body={"gate_id":"UNKNOWN","event":"GOAL","tsf_us":228681597360,"gate_us":5011081595}
#[228682869] [HTTP] POST /api/event from 192.168.0.189 body={"gate_id":"UNKNOWN","event":"GOAL","tsf_us":228682597366,"gate_us":5012081590}
#[228683873] [HTTP] POST /api/event from 192.168.0.189 body={"gate_id":"UNKNOWN","event":"GOAL","tsf_us":228683597364,"gate_us":5013081586}
#[228684866] [HTTP] POST /api/event from 192.168.0.189 body={"gate_id":"UNKNOWN","event":"GOAL","tsf_us":228684597362,"gate_us":5014081581}
#[228685870] [HTTP] POST /api/event from 192.168.0.189 body={"gate_id":"UNKNOWN","event":"GOAL","tsf_us":228685597364,"gate_us":5015081576}
#[228686862] [HTTP] POST /api/event from 192.168.0.189 body={"gate_id":"UNKNOWN","event":"GOAL","tsf_us":228686597358,"gate_us":5016081571}
#[228687868] [HTTP] POST /api/event from 192.168.0.189 body={"gate_id":"UNKNOWN","event":"GOAL","tsf_us":228687597363,"gate_us":5017081566}
#[228688864] [HTTP] POST /api/event from 192.168.0.189 body={"gate_id":"UNKNOWN","event":"GOAL","tsf_us":228688597362,"gate_us":5018081561}
#[228689868] [HTTP] POST /api/event from 192.168.0.189 body={"gate_id":"UNKNOWN","event":"GOAL","tsf_us":228689597358,"gate_us":5019081556}
#[228690864] [HTTP] POST /api/event from 192.168.0.189 body={"gate_id":"UNKNOWN","event":"GOAL","tsf_us":228690597361,"gate_us":5020081551}
#[228691865] [HTTP] POST /api/event from 192.168.0.189 body={"gate_id":"UNKNOWN","event":"GOAL","tsf_us":228691597353,"gate_us":5021081546}
#[228692868] [HTTP] POST /api/event from 192.168.0.189 body={"gate_id":"UNKNOWN","event":"GOAL","tsf_us":228692597361,"gate_us":5022081541}
#[228693866] [HTTP] POST /api/event from 192.168.0.189 body={"gate_id":"UNKNOWN","event":"GOAL","tsf_us":228693597359,"gate_us":5023081536}
#[228694865] [HTTP] POST /api/event from 192.168.0.189 body={"gate_id":"UNKNOWN","event":"GOAL","tsf_us":228694597358,"gate_us":5024081531}
#[228695863] [HTTP] POST /api/event from 192.168.0.189 body={"gate_id":"UNKNOWN","event":"GOAL","tsf_us":228695597360,"gate_us":5025081526}
#[228696860] [HTTP] POST /api/event from 192.168.0.189 body={"gate_id":"UNKNOWN","event":"GOAL","tsf_us":228696597351,"gate_us":5026081521}
#[228697867] [HTTP] POST /api/event from 192.168.0.189 body={"gate_id":"UNKNOWN","event":"GOAL","tsf_us":228697597357,"gate_us":5027081516}
#[228698864] [HTTP] POST /api/event from 192.168.0.189 body={"gate_id":"UNKNOWN","event":"GOAL","tsf_us":228698597357,"gate_us":5028081511}
#[228699865] [HTTP] POST /api/event from 192.168.0.189 body={"gate_id":"UNKNOWN","event":"GOAL","tsf_us":228699597357,"gate_us":5029081506}
#[228700870] [HTTP] POST /api/event from 192.168.0.189 body={"gate_id":"UNKNOWN","event":"GOAL","tsf_us":228700597356,"gate_us":5030081501}
#[228701864] [HTTP] POST /api/event from 192.168.0.189 body={"gate_id":"UNKNOWN","event":"GOAL","tsf_us":228701597354,"gate_us":5031081496}
#[228702869] [HTTP] POST /api/event from 192.168.0.189 body={"gate_id":"UNKNOWN","event":"GOAL","tsf_us":228702597354,"gate_us":5032081491}
#[228703864] [HTTP] POST /api/event from 192.168.0.189 body={"gate_id":"UNKNOWN","event":"GOAL","tsf_us":228703597357,"gate_us":5033081486}
#[228704866] [HTTP] POST /api/event from 192.168.0.189 body={"gate_id":"UNKNOWN","event":"GOAL","tsf_us":228704597355,"gate_us":5034081481}
#[228705863] [HTTP] POST /api/event from 192.168.0.189 body={"gate_id":"UNKNOWN","event":"GOAL","tsf_us":228705597354,"gate_us":5035081476}
#[228706869] [HTTP] POST /api/event from 192.168.0.189 body={"gate_id":"UNKNOWN","event":"GOAL","tsf_us":228706597353,"gate_us":5036081471}
#[228707863] [HTTP] POST /api/event from 192.168.0.189 body={"gate_id":"UNKNOWN","event":"GOAL","tsf_us":228707597353,"gate_us":5037081466}
#[228708873] [HTTP] POST /api/event from 192.168.0.189 body={"gate_id":"UNKNOWN","event":"GOAL","tsf_us":228708597353,"gate_us":5038081461}
#[228709868] [HTTP] POST /api/event from 192.168.0.189 body={"gate_id":"UNKNOWN","event":"GOAL","tsf_us":228709597351,"gate_us":5039081456}
#[228710951] [HTTP] POST /api/event from 192.168.0.189 body={"gate_id":"UNKNOWN","event":"GOAL","tsf_us":228710597352,"gate_us":5040081451}
#[228711863] [HTTP] POST /api/event from 192.168.0.189 body={"gate_id":"UNKNOWN","event":"GOAL","tsf_us":228711597350,"gate_us":5041081446}
#[228712904] [HTTP] POST /api/event from 192.168.0.189 body={"gate_id":"UNKNOWN","event":"GOAL","tsf_us":228712597350,"gate_us":5042081441}
#[228713863] [HTTP] POST /api/event from 192.168.0.189 body={"gate_id":"UNKNOWN","event":"GOAL","tsf_us":228713597349,"gate_us":5043081436}
#[228714883] [HTTP] POST /api/event from 192.168.0.189 body={"gate_id":"UNKNOWN","event":"GOAL","tsf_us":228714597350,"gate_us":5044081431}
#[228715953] [HTTP] POST /api/event from 192.168.0.189 body={"gate_id":"UNKNOWN","event":"GOAL","tsf_us":228715597348,"gate_us":5045081426}
#[228716867] [HTTP] POST /api/event from 192.168.0.189 body={"gate_id":"UNKNOWN","event":"GOAL","tsf_us":228716597348,"gate_us":5046081421}
#[228717868] [HTTP] POST /api/event from 192.168.0.189 body={"gate_id":"UNKNOWN","event":"GOAL","tsf_us":228717597348,"gate_us":5047081416}
#[228718953] [HTTP] POST /api/event from 192.168.0.189 body={"gate_id":"UNKNOWN","event":"GOAL","tsf_us":228718597344,"gate_us":5048081411}
#[228719920] [HTTP] POST /api/event from 192.168.0.189 body={"gate_id":"UNKNOWN","event":"GOAL","tsf_us":228719597347,"gate_us":5049081406}
#[228720874] [HTTP] POST /api/event from 192.168.0.189 body={"gate_id":"UNKNOWN","event":"GOAL","tsf_us":228720597347,"gate_us":5050081401}
#[228721929] [HTTP] POST /api/event from 192.168.0.189 body={"gate_id":"UNKNOWN","event":"GOAL","tsf_us":228721597347,"gate_us":5051081396}
#[228722863] [HTTP] POST /api/event from 192.168.0.189 body={"gate_id":"UNKNOWN","event":"GOAL","tsf_us":228722597339,"gate_us":5052081391}
#[228723878] [HTTP] POST /api/event from 192.168.0.189 body={"gate_id":"UNKNOWN","event":"GOAL","tsf_us":228723597345,"gate_us":5053081386}
#[228724865] [HTTP] POST /api/event from 192.168.0.189 body={"gate_id":"UNKNOWN","event":"GOAL","tsf_us":228724597345,"gate_us":5054081381}
#[228725866] [HTTP] POST /api/event from 192.168.0.189 body={"gate_id":"UNKNOWN","event":"GOAL","tsf_us":228725597344,"gate_us":5055081376}
#[228726862] [HTTP] POST /api/event from 192.168.0.189 body={"gate_id":"UNKNOWN","event":"GOAL","tsf_us":228726597340,"gate_us":5056081370}
#[228727863] [HTTP] POST /api/event from 192.168.0.189 body={"gate_id":"UNKNOWN","event":"GOAL","tsf_us":228727597335,"gate_us":5057081365}
#[228728863] [HTTP] POST /api/event from 192.168.0.189 body={"gate_id":"UNKNOWN","event":"GOAL","tsf_us":228728597342,"gate_us":5058081360}
#[228729864] [HTTP] POST /api/event from 192.168.0.189 body={"gate_id":"UNKNOWN","event":"GOAL","tsf_us":228729597343,"gate_us":5059081355}
#[228730870] [HTTP] POST /api/event from 192.168.0.189 body={"gate_id":"UNKNOWN","event":"GOAL","tsf_us":228730597293,"gate_us":5060081350}
#[228731864] [HTTP] POST /api/event from 192.168.0.189 body={"gate_id":"UNKNOWN","event":"GOAL","tsf_us":228731597342,"gate_us":5061081345}
#[228732874] [HTTP] POST /api/event from 192.168.0.189 body={"gate_id":"UNKNOWN","event":"GOAL","tsf_us":228732597334,"gate_us":5062081340}
#[228733862] [HTTP] POST /api/event from 192.168.0.189 body={"gate_id":"UNKNOWN","event":"GOAL","tsf_us":228733597343,"gate_us":5063081335}
