micromouseonline/kronos/cerberus-gate-controller/firmware/src/race/race-command-source.h

// ----------------------------------------------------------------------------
//  race-command-source.h — Translates raw input from each producer into the
//  race state machine's RaceCommand vocabulary (race-timer.h). One function
//  per source; a source is never faked as another source's payload type just
//  to reuse a sibling function. Local hardware (GPIO/NeoKey/touch) already
//  collapses to a ButtonID in input-events.h, so all three share
//  race_command_from_button() and, through it, BUTTON_COMMAND_MAP below.
//  Serial/HTTP carry data ButtonID can't hold (mouse name, gate_id, remote
//  timestamp) and get their own producer here once those payload types
//  exist (see docs/SYSTEM-DESCRIPTION.md's Serial Protocol section /
//  HTTP server section).
// ----------------------------------------------------------------------------
#pragma once

#include "input-events.h"
#include "net/messages.h"
#include "race-timer.h"
#include "race/system-event-queue.h"

struct ButtonCommandMap {
  RaceCommand on_press;
  RaceCommand on_hold;
};

// One row per ButtonID -- the single place to change what a press or hold
// produces. Applies uniformly to every local producer (GPIO, NeoKey, and
// touch's short presses -- see eez-actions.cpp's action_on_timer_* -- all
// post into the same queue and land here).
//
// ARM's hold is a force-new-mouse override regardless of current race state
// -- RESTART, not NEW_MOUSE, since race_timer_handle_command's WAITING/GOAL
// branches only act on RESTART. TOUCH's hold has no RaceCommand here: on
// GPIO/NeoKey it's a UI-only "return to menu" handled in main.cpp's
// input_event_handler; on the touch panel itself it's a separate
// LVGL-native long-press (action_on_timer_touch_long, eez-actions.cpp)
// that never reaches this table at all.
//
// Reviewed against the state machine, 2026-08-07 -- one action item,
// implemented same day: TOUCH's short press used to map to a bare
// NEW_MOUSE, which race-timer.h deliberately no-ops everywhere (see its
// own comment at the RaceState::WAITING/etc. handlers) -- so it now maps
// to NONE instead (feeds nothing into the RaceCommand pipeline). The
// actual new behaviour lives outside this table, in main.cpp's
// input_event_handler: while the main race screen is showing, a short
// TOUCH press sends `<91,1>` to RATS (MSG_TOUCH_SHORT_PRESS, net/messages.h)
// directly, the same way send_run_time()/ExtraRun already bypass this table
// for host-facing notifications that aren't really race commands. TOUCH's
// hold ("return to menu") is unchanged, already handled the same way.
constexpr ButtonCommandMap BUTTON_COMMAND_MAP[NUM_BUTTONS] = {
    /* BTN_ARM   */ {RaceCommand::ARM, RaceCommand::RESTART},
    /* BTN_START */ {RaceCommand::START, RaceCommand::NONE},
    /* BTN_GOAL  */ {RaceCommand::GOAL, RaceCommand::NONE},
    /* BTN_TOUCH */ {RaceCommand::NONE, RaceCommand::NONE},
};

inline RaceCommand race_command_from_button(ButtonID id, InputEventType type = InputEventType::PRESSED) {
  if (id < 0 || id >= NUM_BUTTONS) {
    return RaceCommand::NONE;
  }
  const ButtonCommandMap &map = BUTTON_COMMAND_MAP[id];
  return (type == InputEventType::HELD) ? map.on_hold : map.on_press;
}

// Parsed by net/serial-protocol.h's line parser from a `<type,value>` wire
// message (see net/messages.h). Defined here, not in serial-protocol.h, so
// this file doesn't need serial-protocol.h to know its own payload type --
// HttpGateEvent will follow the same reasoning once the HTTP producer
// exists. `value` holds the raw text between the comma and '>' -- RATS V2
// (docs/preferredMessageSequencesV2.pdf) carries names/keywords on several
// message types, not just numbers, so the field can't be a plain long
// anymore; see serial_line_value_as_long() below for the numeric ones.
struct SerialLine {
  int type;
  char value[32];
};

inline long serial_line_value_as_long(const SerialLine &line) {
  return strtol(line.value, nullptr, 10);
}

// Host session metadata captured from ContestName/EventName -- purely
// informational (not read by race-timer.h's logic, not enforced against
// anything). AllowedRuns/EntryTimeS live in race-timer.h now instead
// (g_allowed_runs/g_entry_time_s_limit) since race_timer_allowed_runs()
// and the display actually read them.
inline char g_contest_name[32] = "";
inline char g_event_name[32] = "";

inline RaceCommand race_command_from_serial(const SerialLine &line) {
  if (line.type == MSG_NEW_MOUSE) {
    // RESTART, not NEW_MOUSE -- race_timer_handle_command's WAITING/
    // RUNNING/GOAL branches only act on RESTART, same reasoning as
    // BUTTON_COMMAND_MAP's ARM-hold above. This way the host's new-mouse
    // command always takes effect regardless of current race state.
    return RaceCommand::RESTART;
  }
  return RaceCommand::NONE;
}

// Handles every RATS V2 inbound message that ISN'T a race-state transition
// (see race_command_from_serial() above for MSG_NEW_MOUSE, which is).
// ContestName/EventName/AllowedRuns/EntryTimeS are pure metadata capture,
// applied directly here since a benign stale read of race_state (to gate
// them, see below) or a stale write to the target globals is an accepted
// risk already (see race-timer.h's comment on g_allowed_runs/
// g_entry_time_s_limit). SetMode and ExtraRun DO mutate race state
// (race_state/mouse_run_count) -- those go through system_event_post()
// as RaceCommands instead of being applied directly from this RX task, to
// avoid a cross-task write race with the main loop (see
// race_timer_handle_command()'s own comment on ENTER_CALIBRATION/
// RESUME_TIMER/EXTRA_RUN).
inline void serial_protocol_handle_info_message(const SerialLine &line, uint64_t timestamp_us) {
  switch (line.type) {
    case MSG_CONTEST_NAME:
      // docs/RACE-STATE-MACHINE.md: accepted throughout WAITING (host
      // message order isn't guaranteed), ignored in every other state
      // (explicitly "ignored" while ARMED; not specified for
      // CALIBRATE/RUNNING/GOAL, so treated the same -- WAITING is the
      // only state explicitly granted acceptance).
      if (race_state == RaceState::WAITING) {
        strncpy(g_contest_name, line.value, sizeof(g_contest_name) - 1);
        g_contest_name[sizeof(g_contest_name) - 1] = '\0';
      }
      break;
    case MSG_EVENT_NAME:
      if (race_state == RaceState::WAITING) {
        strncpy(g_event_name, line.value, sizeof(g_event_name) - 1);
        g_event_name[sizeof(g_event_name) - 1] = '\0';
      }
      break;
    case MSG_ALLOWED_RUNS:
      if (race_state == RaceState::WAITING) {
        g_allowed_runs = serial_line_value_as_long(line);
      }
      break;
    case MSG_ENTRY_TIME_S:
      if (race_state == RaceState::WAITING) {
        g_entry_time_s_limit = serial_line_value_as_long(line);
      }
      break;
    case MSG_EXTRA_RUN:
      system_event_post(RaceCommand::EXTRA_RUN, timestamp_us);
      break;
    case MSG_SET_MODE:
      if (strcmp(line.value, "CALIBRATION") == 0) {
        system_event_post(RaceCommand::ENTER_CALIBRATION, timestamp_us);
      } else if (strcmp(line.value, "TIMER") == 0) {
        system_event_post(RaceCommand::RESUME_TIMER, timestamp_us);
      } else {
        debug_log_enqueue("[serial] SetMode(%s) unrecognised, ignored", line.value);
      }
      break;
    case MSG_REQUEST_TYPE:
      // CERBERUS's telemetry is C1-only (race-serial-telemetry.h has no
      // C2 messages anywhere), so it always identifies as a 1-channel timer.
      serial_send_message_str(MSG_TIMER_TYPE, "1CH");
      break;
    default:
      break;
  }
}

// Parsed by net/http-server.h's POST /api/event JSON handler (DESIGN-
// REQUIREMENT.md's Asynchronous HTTP Listener). gate_id is carried through
// unchanged into SystemEvent::payload (the same field NEW_MOUSE's mouse
// name would use); event is looked up in HTTP_EVENT_COMMAND_MAP below.
struct HttpGateEvent {
  char gate_id[32];
  char event[16];
  uint64_t tsf_us;
  uint64_t gate_us;
};

struct HttpEventCommandMap {
  const char *name;
  RaceCommand command;
};

// One row per accepted `event` string -- mirrors BUTTON_COMMAND_MAP's "one
// place to change what a source produces" role, just keyed by name instead
// of ButtonID since a remote gate has no button to press. RESTART is
// reachable here (unlike from a physical button, see BUTTON_COMMAND_MAP's
// comment) -- it has no dedicated physical button and is only raised via
// serial or HTTP command.
// The "NEW_MOUSE" event string maps to RaceCommand::RESTART -- same
// reasoning as BUTTON_COMMAND_MAP's ARM-hold and race_command_from_serial's
// <98,0> handling above: race_timer_handle_command's WAITING/RUNNING/GOAL
// branches only act on RESTART, so this is what makes an HTTP new-mouse
// request take effect regardless of current race state, matching the other
// two producers.
constexpr HttpEventCommandMap HTTP_EVENT_COMMAND_MAP[] = {
    {"ARM", RaceCommand::ARM},         {"START", RaceCommand::START},       {"GOAL", RaceCommand::GOAL},
    {"RESTART", RaceCommand::RESTART}, {"NEW_MOUSE", RaceCommand::RESTART},
};

inline RaceCommand race_command_from_http(const HttpGateEvent &evt) {
  for (const auto &row : HTTP_EVENT_COMMAND_MAP) {
    if (strcmp(evt.event, row.name) == 0) {
      return row.command;
    }
  }
  return RaceCommand::NONE;  // unrecognised `event` value
}

struct HttpInfoMessageMap {
  const char *name;
  int type;  // one of net/messages.h's MessageType inbound values
};

// HTTP equivalents of every RATS V2 inbound message serial_protocol_handle_
// info_message() above already handles, for hosts that talk HTTP instead of
// the legacy UART wire. Keyed by name (there's no UART `<type,value>` framing
// over HTTP), not by MessageType's numeric code -- mirrors
// HTTP_EVENT_COMMAND_MAP's name-keyed shape just above.
constexpr HttpInfoMessageMap HTTP_INFO_MESSAGE_MAP[] = {
    {"CONTEST_NAME", MSG_CONTEST_NAME}, {"EVENT_NAME", MSG_EVENT_NAME}, {"ALLOWED_RUNS", MSG_ALLOWED_RUNS}, {"ENTRY_TIME_S", MSG_ENTRY_TIME_S},
    {"EXTRA_RUN", MSG_EXTRA_RUN},       {"SET_MODE", MSG_SET_MODE},     {"REQUEST_TYPE", MSG_REQUEST_TYPE},
};

/// @brief Looks up an HTTP `event` name against HTTP_INFO_MESSAGE_MAP.
/// @return the matching MessageType, or -1 if `event` isn't one of these.
inline int http_info_message_type(const char *event_name) {
  for (const auto &row : HTTP_INFO_MESSAGE_MAP) {
    if (strcmp(event_name, row.name) == 0) {
      return row.type;
    }
  }
  return -1;
}
