micromouseonline/kronos/hesperus-timing-gate/firmware/src/debug-log.h

// ----------------------------------------------------------------------------
//  debug-log.h — Shared debug output, mirrors
//  cerberus-gate-controller/src/debug-log.h's shape. Every line is prefixed
//  with the current Wi-Fi TSF counter (ms) -- hesperus and cerberus are both
//  stations on the same AP, so this is a shared, sub-ms-precision clock
//  across boards (already used for gate-event timing), letting logs from
//  different boards be interleaved into a true event order after the fact.
//  Only meaningful once Wi-Fi/beacon sync has occurred; lines logged before
//  then (early boot) show a small/near-zero value.
//
//  serial_write_mutex guards every write to Serial -- multiple producers
//  call these (uploadWorkerTask, heartbeatTimerCallback's FreeRTOS timer
//  context, loop() itself), and an unguarded interleaved write can corrupt
//  or split a line. No queued/async variant like cerberus's
//  debug_log_enqueue() -- nothing on hesperus is response-latency-sensitive
//  to a blocking Serial write the way cerberus's HTTP handler was.
//
//  debug_log_line_hook, if set, is called with each fully-assembled
//  "[T=...] message" line (no trailing newline) from inside the same
//  serial_write_lock()/unlock() section used for the Serial write -- see
//  net/debug-http-server.h, which registers it to capture recent lines into
//  an in-RAM ring buffer for the /logs diagnostics endpoint. Null by
//  default; this header has no dependency on that one.
// ----------------------------------------------------------------------------
#pragma once

#include <Arduino.h>
#include <esp_wifi.h>
#include <freertos/FreeRTOS.h>
#include <freertos/semphr.h>
#include <stdarg.h>
#include <stdio.h>

// Compile-time gate for routine per-WS-event logging (the "Sent"/
// "WS-ACK-RECV" lines that fire on every single event even when nothing is
// wrong) -- off by default to keep normal operation quiet. Flip to 1 (or
// pass -D WS_EVENT_LOG_DETAIL=1 via platformio.ini build_flags) and rebuild
// for a dedicated diagnostic trial; this is the exact instrumentation
// NETWORK-TIMING-LOG.md's retry/latency investigations have relied on, kept
// available rather than deleted. Anomaly lines (Resent/dropped/blocked/link
// down) stay unconditional -- they're already low-frequency and valuable
// whenever they do fire.
#ifndef WS_EVENT_LOG_DETAIL
#define WS_EVENT_LOG_DETAIL 0
#endif

inline SemaphoreHandle_t serial_write_mutex = xSemaphoreCreateMutex();

inline void serial_write_lock() {
  xSemaphoreTake(serial_write_mutex, portMAX_DELAY);
}
inline void serial_write_unlock() {
  xSemaphoreGive(serial_write_mutex);
}

inline uint64_t debug_timestamp_ms() {
  return esp_wifi_get_tsf_time(WIFI_IF_STA) / 1000;
}

inline void (*debug_log_line_hook)(const char *line) = nullptr;

/// @brief Writes one already-timestamp-prefixed, newline-free line to
/// Serial and forwards it to debug_log_line_hook if set. Shared by
/// debug_println()/debug_printf() so both go through one Serial write and
/// one hook call per line.
inline void debug_log_emit(const char *line) {
  serial_write_lock();
  Serial.println(line);
  serial_write_unlock();
  if (debug_log_line_hook) {
    debug_log_line_hook(line);
  }
}

template <typename T>
inline void debug_println(T value) {
  char prefix[32];
  snprintf(prefix, sizeof(prefix), "[T=%llums] ", debug_timestamp_ms());
  String line = prefix;
  line += value;
  debug_log_emit(line.c_str());
}

inline void debug_printf(const char *fmt, ...) {
  char buf[160];
  va_list args;
  va_start(args, fmt);
  vsnprintf(buf, sizeof(buf), fmt, args);
  va_end(args);
  size_t len = strlen(buf);
  if (len > 0 && buf[len - 1] == '\n') {
    buf[len - 1] = '\0';  // debug_log_emit's println supplies the newline
  }
  char prefix[32];
  snprintf(prefix, sizeof(prefix), "[T=%llums] ", debug_timestamp_ms());
  String line = prefix;
  line += buf;
  debug_log_emit(line.c_str());
}
