micromouseonline/kronos/cerberus-gate-controller/firmware/src/race/system-event-queue.h

// ----------------------------------------------------------------------------
//  system-event-queue.h — Main Event Queue for remote (Serial/HTTP)
//  producers, feeding the same race_timer_handle_command() entry point that
//  local buttons already call directly (see main.cpp's input_event_handler).
//  Local buttons are NOT rerouted through this queue -- both paths converge
//  on the same state machine, so it doesn't need to know which queue an
//  event came from. Same producer/consumer shape as input-events.h's
//  xInputQueue, applied to SystemEvent instead of InputEvent.
// ----------------------------------------------------------------------------
#pragma once

#include <Arduino.h>
#include <esp_timer.h>
#include <freertos/FreeRTOS.h>
#include <freertos/queue.h>

#include "race-timer.h"

struct SystemEvent {
  RaceCommand type;
  uint64_t timestamp_us;
  // Mouse name (RaceCommand::RESTART's payload, from a RATS V2 NewMouse
  // line) or gate_id (HTTP), depending on source -- payload_is_mouse_name
  // disambiguates which, since main.cpp's system_event_handler() is the
  // single consumer for every source and can't otherwise tell them apart.
  char payload[32];
  bool payload_is_mouse_name = false;
};

inline QueueHandle_t xSystemEventQueue = nullptr;

inline void system_event_queue_init() {
  xSystemEventQueue = xQueueCreate(32, sizeof(SystemEvent));
}

// Thread/ISR-safe producer, usable from the Serial RX task, the HTTP
// server's own task, or an ISR context via xQueueSendFromISR.
inline void system_event_post(RaceCommand type, uint64_t timestamp_us, const char *payload = "",
                               bool payload_is_mouse_name = false) {
  SystemEvent evt{};
  evt.type = type;
  evt.timestamp_us = timestamp_us;
  strncpy(evt.payload, payload, sizeof(evt.payload) - 1);
  evt.payload_is_mouse_name = payload_is_mouse_name;
  if (xSystemEventQueue != nullptr) {
    xQueueSend(xSystemEventQueue, &evt, 0);
  }
}

// Call once per loop() iteration. Drains all pending events (non-blocking).
inline void system_event_queue_drain(void (*handler)(const SystemEvent &) = nullptr) {
  if (xSystemEventQueue == nullptr) {
    return;
  }
  SystemEvent evt;
  while (xQueueReceive(xSystemEventQueue, &evt, 0) == pdTRUE) {
    if (handler != nullptr) {
      handler(evt);
    }
  }
}
