micromouseonline/kronos/cerberus-gate-controller/firmware/src/display/touch-calibration.h

#pragma once

#include <Arduino.h>
#include <Preferences.h>
#include "debug-log.h"
#include "display.h"

// Gated per-board by TOUCH_NEEDS_CALIBRATION (lib/boards/*.h). Originally
// resistive-only (XPT2046's raw ADC readings need linear mapping to screen
// pixels) -- also required on capacitive boards now: a capacitive chip
// reports pixel coordinates in its own native orientation, but if that
// doesn't match the panel's LCD_ROTATION, touches land in the wrong place
// (found on Freenove; see INPUT-SYSTEM.md). lcd.calibrateTouch()'s
// 4-corner wizard is technology-agnostic -- it captures whatever mapping is
// needed from raw-reported to actual-screen position, so it fixes rotation
// offset the same way it fixes resistive scaling. Callers must still guard
// with #if HAS_TOUCH_INPUT && TOUCH_NEEDS_CALIBRATION (see main.cpp) since
// setTouchCalibrate() dereferences the touch driver unconditionally and
// will crash on a board with no touch controller (e.g. M5 Core).

inline Preferences prefs;
inline uint16_t touchCalData[8];
const char* PREFS_NAMESPACE = "touch-cal";

/**
 * Triggers the library's built-in calibration wizard, saves the resulting
 * calibration data array directly to NVS, and applies it.
 */
inline void re_calibrate(LGFX& lcd) {
  // 1. Wipe old calibration from NVS
  prefs.begin(PREFS_NAMESPACE, false);
  prefs.clear();

  debug_log_enqueue("Starting native LovyanGFX calibration wizard...");

  // 2. Clear screen and display basic instructions
  lcd.fillScreen(TFT_BLACK);
  lcd.setTextColor(TFT_WHITE);
  lcd.setTextSize(2);
  lcd.drawCenterString("Touch Calibration", lcd.width() / 2, lcd.height() / 2 - 20);

  // 3. Let LovyanGFX run its native 4-corner calibration routine
  // Parameters: (data_storage_array, color_of_target, color_of_bg, size_of_target)
  lcd.calibrateTouch(touchCalData, TFT_RED, TFT_BLACK, 15);

  // 4. Activate the calibration immediately
  lcd.setTouchCalibrate(touchCalData);

  // 5. Save the calibration data block to Preferences
  prefs.putBytes("cal_data", touchCalData, sizeof(touchCalData));
  prefs.putBool("calibrated", true);
  prefs.end();

  lcd.fillScreen(TFT_BLACK);
  lcd.drawCenterString("Calibration Saved!", lcd.width() / 2, lcd.height() / 2);
  delay(1000);
}

/**
 * Checks for existing calibration. Loads it if found,
 * otherwise kicks off a fresh calibration process.
 */
inline void calibrate(LGFX& lcd) {
  prefs.begin(PREFS_NAMESPACE, true);  // Open in read-only mode
  bool isCalibrated = prefs.getBool("calibrated", false);

  if (isCalibrated) {
    // Read the array block directly back into memory
    prefs.getBytes("cal_data", touchCalData, sizeof(touchCalData));
    prefs.end();

    // Apply it to the display instance
    lcd.setTouchCalibrate(touchCalData);
    debug_log_enqueue("Native touch calibration loaded successfully.");
  } else {
    prefs.end();
    debug_log_enqueue("No calibration data found. Launching wizard...");
    re_calibrate(lcd);
  }
}
